OpenARDF/SignalSlinger/Software/AVR128DA28/SignalSlinger/main.cpp

/*
 *  MIT License
 *
 *  Copyright (c) 2026 DigitalConfections
 *
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
 *  THE SOFTWARE IS PROVIDED "AS IS", WITHOUT WARRANTY OF ANY KIND, EXPRESS OR
 *  IMPLIED, INCLUDING BUT NOT LIMITED TO THE WARRANTIES OF MERCHANTABILITY,
 *  FITNESS FOR A PARTICULAR PURPOSE AND NONINFRINGEMENT. IN NO EVENT SHALL THE
 *  AUTHORS OR COPYRIGHT HOLDERS BE LIABLE FOR ANY CLAIM, DAMAGES OR OTHER
 *  LIABILITY, WHETHER IN AN ACTION OF CONTRACT, TORT OR OTHERWISE, ARISING FROM,
 *  OUT OF OR IN CONNECTION WITH THE SOFTWARE OR THE USE OR OTHER DEALINGS IN THE
 *  SOFTWARE.
 */

#include "serial_latency.h"
#include "atmel_start.h"
#include <avr/io.h>
#include <avr/interrupt.h>
#include <string.h>
#include <time.h>
#include <stdio.h>
#include <stdlib.h>
#include <ctype.h>
#include <avr/sleep.h>
#include <atomic.h>
#include <math.h>

#include "serialbus.h"
#include "transmitter.h"
#include "morse.h"
#include "adc.h"
#include "external_battery_feedback.h"
#include "util.h"
#include "eeprommanager.h"
#include "binio.h"
#include "leds.h"
#include "CircularStringBuff.h"
#include "globals.h"
#include "shared_state.h"
#include "thermal_shutdown.h"
#include "session_history.h"
#include "rtc.h"
#include "rstctrl.h"

#include <cpuint.h>
#include <ccp.h>

/*
 * Main firmware orchestration for SignalSlinger.
 *
 * This module owns the top-level runtime state, interrupt handlers, event
 * engine coordination, user interaction flow, and serial command handling that
 * ties the rest of the firmware together.
 *
 * Lower-level hardware drivers and focused utility logic belong in their own
 * modules; this file is where those pieces are sequenced into device behavior.
 */

/***********************************************************************
 * Local Typedefs
 ************************************************************************/

/* Select how watchdog-related resets should be handled. */
typedef enum
{
	WD_SW_RESETS,
	WD_HW_RESETS,
	WD_FORCE_RESET,
	WD_DISABLE
} WDReset;

/* Record what caused the device to wake or start running. */
typedef enum
{
	AWAKENED_INIT,
	POWER_UP_START,
	AWAKENED_BY_CLOCK,
	AWAKENED_BY_BUTTONPRESS,
	AWAKENED_BY_SERIAL_PORT
} Awakened_t;

/* Track missing hardware discovered during startup or runtime checks. */
typedef enum
{
	HARDWARE_OK,
	HARDWARE_NO_RTC = 0x01,
	HARDWARE_NO_SI5351 = 0x02
} HardwareError_t;

static bool evaluateThermalShutdownState(float processor_temperature, bool current_state);
static uint16_t adcConversionPeriodTicks(uint8_t channel_index);
static void updateTemperatureState(float temperature);
static void turnCoolingFanOffForSleep(void);
static float sampleTemperatureNow(void);
static bool resetProcessorTemperatureExtremesToCurrent(float *temperature_out);
static bool resetProcessorMaxEverTemperatureToCurrent(float *temperature_out);

/* Track the current step in the serial cloning/synchronization exchange. */
typedef enum
{
	SYNC_Searching_for_slave,
	SYNC_Waiting_for_FUN_A_reply,
	SYNC_Align_to_Second_Transition,
	SYNC_Waiting_for_CLK_T_reply,
	SYNC_Waiting_for_CLK_S_reply,
	SYNC_Waiting_for_CLK_F_reply,
	SYNC_Waiting_for_CLK_D_reply,
	SYNC_Waiting_for_ID_reply,
	SYNC_Waiting_for_ID_CodeSpeed_reply,
	SYNC_Waiting_for_Pattern_CodeSpeed_reply,
	SYNC_Waiting_for_EVT_reply,
	SYNC_Waiting_for_NoEvent_Freq_reply,
	SYNC_Waiting_for_Freq_Low_reply,
	SYNC_Waiting_for_Freq_Med_reply,
	SYNC_Waiting_for_Freq_Hi_reply,
	SYNC_Waiting_for_Freq_Beacon_reply,
	// 	SYNC_Waiting_for_PAT_A_reply,
	// 	SYNC_Waiting_for_PAT_B_reply,
	// 	SYNC_Waiting_for_PAT_C_reply,
	// 	SYNC_Waiting_for_FRE_A_reply,
	// 	SYNC_Waiting_for_FRE_B_reply,
	// 	SYNC_Waiting_for_FRE_C_reply,
	SYNC_Waiting_for_ACK
} SyncState_t;

/* Preserve the event window that should be restored after clone mode exits. */
typedef struct
{
	time_t event_start_epoch;
	time_t event_finish_epoch;
	uint8_t days_to_run;
} CloneTimingSnapshot_t;

#define PROGRAMMING_MESSAGE_TIMEOUT_PERIOD 3000
#define WAKE_AUTH_HOLD_TICKS 600
#define BOOTLOADER_WAKE_AUTH_CREDIT_TICKS 420
#define BUTTON_HOLD_PREVIEW_SAMPLE_TICKS 50
#define BUTTON_LONG_PRESS_SAMPLE_TICKS 200
#define STARTUP_SWITCH_SETTLE_SAMPLE_COUNT 12
#define STARTUP_SWITCH_SETTLE_DELAY_MS 5
#define SIGNALSLINGER_BOOT_HANDOFF_POWER_BUTTON_HELD 0x53U
#define SIGNALSLINGER_BOOT_APP_UPDATE_REQUEST 0xA5U
#define SIGNALSLINGER_BOOT_HANDOFF_INFO_MAGIC 0xB0U
#define SIGNALSLINGER_BOOT_HANDOFF_INFO_MAGIC_MASK 0xF0U
#define SIGNALSLINGER_BOOT_HANDOFF_INFO_PROTOCOL_MASK 0x0FU
#define SIGNALSLINGER_BOOT_HANDOFF_UNAVAILABLE 0xFFU

/***********************************************************************
 * Global Variables & String Constants
 *
 * Identify each global with a "g_" prefix
 * Whenever possible limit globals' scope to this file using "static"
 * Use "volatile" for globals shared between ISRs and foreground
 ************************************************************************/
#define TEMP_STRING_SIZE 50
static char g_tempStr[TEMP_STRING_SIZE + 1] = {'\0'};
static uint8_t g_bootloader_protocol = SIGNALSLINGER_BOOT_HANDOFF_UNAVAILABLE;
static uint8_t g_bootloader_version_major = SIGNALSLINGER_BOOT_HANDOFF_UNAVAILABLE;
static uint8_t g_bootloader_version_minor = SIGNALSLINGER_BOOT_HANDOFF_UNAVAILABLE;

volatile bool g_device_enabled = false;

static volatile bool g_foreground_start_event = false;
static volatile bool g_foreground_enable_transmitter = false;
static volatile int g_hardware_error = (int)HARDWARE_OK;
static volatile bool g_defer_cloned_event_start = false;

/* Variables related to the "Event Engine" which consists of two ISRs and the foreground working
together to handle event timing. Communication between ISRs and forground is most efficiently
handled using volatile global variables. */
static volatile int32_t g_evteng_on_the_air = 0;
static volatile int g_evteng_sendID_seconds_countdown = 0;
static volatile uint16_t g_evteng_code_throttle = 50;
static volatile uint16_t g_evteng_sleepshutdown_seconds = 300;
volatile uint8_t g_evteng_id_codespeed = EEPROM_ID_CODE_SPEED_DEFAULT;
volatile uint8_t g_evteng_pattern_codespeed = EEPROM_PATTERN_CODE_SPEED_DEFAULT;
volatile int16_t g_evteng_on_air_seconds = EEPROM_ON_AIR_TIME_DEFAULT;   /* amount of time to spend on the air */
volatile int16_t g_evteng_off_air_seconds = EEPROM_OFF_AIR_TIME_DEFAULT; /* amount of time to wait before returning to the air */

/**
 * Update the system clock, optionally re-zeroing the external RTC at the same time.
 *
 * The foreground uses this helper when a clock-setting operation must keep the
 * software time base and the hardware RTC aligned through one critical section.
 *
 * @param epoch New epoch value to install.
 * @param reset_rtc true to zero the RTC counter before updating system time.
 */
static inline void atomic_set_system_time(time_t epoch, bool reset_rtc)
{
	ENTER_CRITICAL(main_set_system_time);
	if(reset_rtc)
	{
		RTC_zero();
	}
	set_system_time(epoch);
	EXIT_CRITICAL(main_set_system_time);
}
volatile int16_t g_evteng_intra_cycle_delay_time = EEPROM_INTRA_CYCLE_DELAY_TIME_DEFAULT; /* offset time into a repeating transmit cycle */
volatile int16_t g_evteng_ID_period_seconds = EEPROM_ID_TIME_INTERVAL_DEFAULT;            /* amount of time between ID/callsign transmissions */
volatile time_t g_event_start_epoch = EEPROM_START_TIME_DEFAULT;
volatile time_t g_evteng_loaded_start_epoch = 0;
volatile time_t g_event_finish_epoch = EEPROM_FINISH_TIME_DEFAULT;
volatile time_t g_evteng_loaded_finish_epoch = 0;
volatile bool g_evteng_event_enabled = EEPROM_EVENT_ENABLED_DEFAULT; /* indicates that the conditions for executing the event are set */
volatile bool g_evteng_event_commenced = false;
volatile bool g_evteng_sending_station_ID = false; /* Allows a small extension of transmissions to ensure the ID is fully sent */
static volatile bool g_evteng_run_event_until_canceled = false;
volatile bool g_evteng_initialize_event = false;

/* Various other functions handled in ISRs are most efficiently handled (with care) by volatile
globals. */
volatile float g_internal_voltage_low_threshold = EEPROM_INT_BATTERY_LOW_THRESHOLD_V;
volatile float g_internal_bat_voltage = 0.;
volatile bool g_internal_bat_detected = false;
volatile int8_t g_thermal_shutdown_threshold = EEPROM_THERMAL_SHUTDOWN_THRESHOLD_DEFAULT;
volatile bool g_thermal_shutdown_enabled = EEPROM_THERMAL_SHUTDOWN_ENABLED_DEFAULT;
volatile float g_external_voltage = 0.;
volatile float g_processor_temperature = MINIMUM_VALID_TEMP - 1.;
volatile float g_processor_min_temperature = MAXIMUM_VALID_TEMP + 1.;
volatile float g_processor_max_temperature = MINIMUM_VALID_TEMP - 1.;
volatile float g_processor_max_ever_temperature = EEPROM_PROCESSOR_MAX_EVER_TEMPERATURE_DEFAULT;
volatile bool g_restart_conversions = false;
volatile bool g_seconds_transition = false;
volatile bool g_muteAfterID = false; /* Inhibit any transmissions after the ID has been sent */
volatile uint32_t g_event_checksum = 0;
volatile uint8_t g_days_to_run = 1;
volatile uint8_t g_schedule_day_index = 0;
volatile Function_t g_function = Function_ARDF_TX;
volatile uint8_t g_foxoring_pattern_codespeed = EEPROM_FOXORING_PATTERN_CODESPEED_DEFAULT;
volatile uint16_t g_time_needed_for_ID = 0;
char g_messages_text[STATION_ID + 1][MAX_PATTERN_TEXT_LENGTH + 2];

static volatile bool g_go_to_sleep_now = false;
static volatile bool g_sleeping = false;
static volatile time_t g_time_to_wake_up = 0;
static volatile Awakened_t g_awakenedBy = POWER_UP_START;
static volatile SleepType g_sleepType = SLEEP_FOREVER;
static volatile uint8_t g_button_wake_prior_sleep_type = SLEEP_FOREVER;
static volatile bool g_button_wake_prior_event_enabled = false;
static volatile bool g_button_wake_prior_event_commenced = false;
static volatile time_t g_seconds_since_wakeup = 0;
static volatile bool g_foreground_check_for_long_wakeup_press = false;
static volatile bool g_ignore_sleep_button_wake_until_release = false;
static volatile bool g_device_wakeup_complete = false;
static volatile bool g_foreground_enable_serialbus = false;
static volatile bool g_charge_battery = false;
static volatile bool g_turn_on_fan = false;
static volatile bool g_foreground_report_settings = false;
static volatile uint16_t g_report_settings_countdown = 0;
static bool g_event_launched_by_user_action = false;
static bool g_start_event_after_keydown = false; /* Foreground-only: one-press keydown should launch a synced event afterward */

/* Foreground-only interaction helpers:
 * - g_consume_current_press_for_led_wake prevents the first press after LED timeout
 *   from being interpreted as a command.
 * - g_pending_led_revival requests that foreground restore LED indications.
 * - g_event_canceled_by_user latches cancellation of the current event window until
 *   the user explicitly restarts it or the schedule advances to a new window.
 */
static volatile bool g_consume_current_press_for_led_wake = false;
static volatile bool g_pending_led_revival = false;
static volatile bool g_event_canceled_by_user = false;
/* Calibration consumes the first debounced edge immediately so a press cannot
 * also become an event command, LED wake, multi-press, or long-hold action. */
static volatile bool g_consume_current_press_for_calibration_exit = false;
static volatile bool g_foreground_exit_calibration = false;
static volatile bool g_button_hold_preview_active = false;

/* Preserve the intent of the press even if a test expires or a scheduled start
 * arrives while the user is still holding the button. */
enum ButtonHoldIntent { BUTTON_HOLD_DEFAULT, BUTTON_HOLD_STOP_TEST, BUTTON_HOLD_SLEEP_SCHEDULE };
static volatile uint8_t g_button_hold_intent = BUTTON_HOLD_DEFAULT;
static volatile uint8_t g_long_button_hold_intent = BUTTON_HOLD_DEFAULT;

#define NUMBER_OF_POLLED_ADC_CHANNELS 3
#define ADC_CONVERSION_TIMEOUT_TICKS 10
static ADC_Active_Channel_t g_adcChannelOrder[NUMBER_OF_POLLED_ADC_CHANNELS] = {ADCInternalBatteryVoltage, ADCExternalBatteryVoltage, ADCTemperature};
static volatile uint16_t g_adcCountdownCount[NUMBER_OF_POLLED_ADC_CHANNELS] = {2000, 2000, 4000};
static volatile uint16_t g_lastConversionResult[NUMBER_OF_POLLED_ADC_CHANNELS] = {0, 0, 0};
static ExternalBatteryFeedback g_external_battery_feedback;

/* Release only the awake measurement client, preserving charge/transmit demand.
 * Called with interrupts masked at sleep entry and by the ADC service ISR.
 */
static void cancelExternalBatteryFeedback(void)
{
	g_external_battery_feedback.reset();
	setExtBatLoadSwitch(OFF, BATTERY_MEASUREMENT);
}

static volatile bool g_thermal_shutdown = false;

volatile uint16_t g_foreground_handle_counted_presses = 0;
volatile uint16_t g_switch_presses_count = 0;
volatile bool g_long_button_press = false;
volatile uint16_t g_button_hold_countdown;

#define NUMBER_OF_TEST_FREQUENCIES (4)
uint8_t g_frequency_to_test = NUMBER_OF_TEST_FREQUENCIES;

static volatile uint16_t g_programming_countdown = 0;
static volatile uint16_t g_programming_msg_throttle = 0;
static volatile uint16_t g_send_clone_success_countdown = 0;
static SyncState_t g_programming_state = SYNC_Searching_for_slave;
static CloneTimingSnapshot_t g_clone_timing_snapshot = {0, 0, 1};
volatile bool g_cloningInProgress = false;

volatile Enunciation_t g_enunciator = LED_ONLY;
static volatile uint16_t g_key_down_countdown = 0;
static volatile bool g_foreground_reset_after_keydown = false;
static volatile uint16_t g_demo_event_countdown = 0;
static volatile bool g_foreground_reset_after_demo = false;

leds LEDS = leds();
CircularStringBuff g_text_buff(TEXT_BUFF_SIZE);

EepromManager g_ee_mgr;

volatile bool g_isMaster = false;
volatile uint16_t isMasterCountdownSeconds = 0;
Fox_t g_fox[EVENT_NUMBER_OF_EVENTS] = {FOX_1, SPRINT_S1, FOXORING_FOX1}; /* classic, sprint, foxoring */

Event_t g_event = EEPROM_EVENT_SETTING_DEFAULT;
Frequency_Hz g_frequency = EEPROM_FREQUENCY_DEFAULT;
Frequency_Hz g_frequency_low = EEPROM_FREQUENCY_LOW_DEFAULT;
Frequency_Hz g_frequency_med = EEPROM_FREQUENCY_MED_DEFAULT;
Frequency_Hz g_frequency_hi = EEPROM_FREQUENCY_HI_DEFAULT;
Frequency_Hz g_frequency_beacon = EEPROM_FREQUENCY_BEACON_DEFAULT;

int8_t g_utc_offset;
uint8_t g_unlockCode[UNLOCK_CODE_SIZE + 2];

volatile bool g_enable_manual_transmissions = true;
static volatile bool g_meshmode = false;

typedef enum
{
	FREQ_SOURCE_CURRENT,
	FREQ_SOURCE_LOW,
	FREQ_SOURCE_MED,
	FREQ_SOURCE_HIGH,
	FREQ_SOURCE_BEACON
} FrequencySource_t;

static const char *const g_fixed_fox_pattern_text[USE_CURRENT_FOX] =
    {
        "MO",
        "MOE",
        "MOI",
        "MOS",
        "MOH",
        "MO5",
        "S",
        "ME",
        "MI",
        "MS",
        "MH",
        "M5",
        "OE",
        "OI",
        "OS",
        "OH",
        "O5",
        NULL,
        NULL,
        NULL,
        NULL};

static const FrequencySource_t g_fox_frequency_source[USE_CURRENT_FOX] =
    {
        FREQ_SOURCE_BEACON,
        FREQ_SOURCE_LOW,
        FREQ_SOURCE_LOW,
        FREQ_SOURCE_LOW,
        FREQ_SOURCE_LOW,
        FREQ_SOURCE_LOW,
        FREQ_SOURCE_MED,
        FREQ_SOURCE_LOW,
        FREQ_SOURCE_LOW,
        FREQ_SOURCE_LOW,
        FREQ_SOURCE_LOW,
        FREQ_SOURCE_LOW,
        FREQ_SOURCE_HIGH,
        FREQ_SOURCE_HIGH,
        FREQ_SOURCE_HIGH,
        FREQ_SOURCE_HIGH,
        FREQ_SOURCE_HIGH,
        FREQ_SOURCE_LOW,
        FREQ_SOURCE_MED,
        FREQ_SOURCE_HIGH,
        FREQ_SOURCE_LOW};

static const char *const g_frequency_test_pattern_text[NUMBER_OF_TEST_FREQUENCIES] =
    {
        "< E<",
        "< EE<",
        "< EEE<",
        "< EEEE<"};

/***********************************************************************
 * Private Function Prototypes
 *
 * These functions are available only within this file
 ************************************************************************/
void handle_1sec_tasks(void);
bool loadedEventShouldBeEnabled(void);
void handleSerialBusMsgs(void);
uint16_t throttleValue(uint8_t speed);
bool activateEventEngineUsingCurrentSettings(time_t startTime, time_t finishTime);
bool launchLoadedEvent(void);
void reportSettings(void);
uint16_t timeNeededForID(void);
Frequency_Hz getFrequencySetting(void);
bool syncCurrentFrequencySetting(bool leaveClockOff);
bool refreshCurrentFrequencySetting(Frequency_Hz previousFrequency, bool leaveClockOff);
char *getCurrentPatternText(void);
int getPatternCodeSpeed(void);
int getFoxCodeSpeed(void);
Fox_t getFoxSetting(void);
void handleSerialCloning(void);
bool timeIsSet(void);
bool eventIsScheduledToRun(time_t *start_epoch, time_t *finish_epoch);
bool eventIsScheduledToRun(volatile time_t *start_epoch, volatile time_t *finish_epoch);
bool eventIsScheduledToRunNow(time_t start_epoch, time_t finish_epoch);
bool eventScheduledForTheFuture(time_t start_epoch, time_t finish_epoch);
bool noEventWillRun(void);
bool eventRunning(void);
void restoreStateAfterButtonWakeAuthorization(void);
static void restoreEventAfterWakeAuthorization(void);
static bool shouldRestoreTransmitterForSleepContext(SleepType sleepType);
static const char *hardwareBuildString(void);
static void sendFirmwareInfo(void);
static inline void captureButtonWakeFromSleep(void);
static inline void clearPendingWakeInterruptFlags(void);
static inline void setWakeAuthorizationLedPinsOn(void);
static inline void bootloaderHandoffCaptureInfo(void);
static inline bool bootloaderHandoffReportedPowerButtonHeld(void);
static inline bool bootloaderHandoffInfoAvailable(void);
static inline bool coldStartLedFeedbackShouldStayOn(bool bootloader_power_button_held);
static inline uint16_t initialWakeAuthorizationTicks(bool bootloader_power_button_held);
static void serviceColdStartButtonDuringStartup(bool *button_held_closed);
static inline void setButtonHoldPreviewIndicator(bool active);
static void refreshProcessorMaxEverTemperature(void);
bool shouldPowerTransmitterAfterWake(void);
void configRedLEDforEvent(void);
bool switchIsClosed(void);
static inline bool rawSwitchIsClosed(void);
static bool switchIsClosedAtStartup(void);
static inline void configureSwitchInterruptForAwake(void);
static inline void configureSwitchInterruptForSleepWake(void);
bool allClocksSet(Settings_t location);
ConfigurationState_t clockConfigurationCheck(Settings_t location);
bool startEvent(void);
static bool foxUsesFastCodeSpeed(Event_t event, Fox_t fox);

/*******************************/
/* Hardcoded event support     */
/*******************************/
void suspendEvent(SessionReason reason = REASON_SETTINGS);
void startEventNow(bool configOverride);
void startSyncdEventNow(bool configOverride);
bool startEventUsingRTC(void);
void startTransmissionsNow(bool configOverride);
void setupForFox(Fox_t fox, EventAction_t action);
time_t validateTimeString(char *str, char *errMsg);
time_t validateTimeString(char *str, volatile time_t *epochVar, bool align5min, char *errMsh);
time_t validateTimeString(char *str, volatile time_t *epochVar, bool align5min, char *errMsg, const char *rawInput);
bool reportTimeTill(time_t from, time_t until, const char *prefix, const char *failMsg);
void reportConfigErrors(Settings_t location);
/*******************************/
/* End hardcoded event support */
/*******************************/

static void loadCurrentPatternMorse(bool *repeat, callerID_t caller);
static void loadStationIDMorse(bool *repeat, callerID_t caller);
static void refreshActiveAutomatedPattern(void);
static const char *completeTimeString_volatile(const char *partialString, volatile time_t *currentEpoch);
static bool parseClockHourMinuteOffset(const char *offsetString, uint16_t *hours, uint8_t *minutes, bool *hasMinutes);
static time_t alignEpochToNearestBoundary(time_t epoch, time_t boundary, time_t minimumEpoch);
static bool resolveClockOffsetToEpoch(const char *offsetString, time_t baseEpoch, const char *baseEpochError, bool suppressBaseEpochError, time_t hourBoundary, time_t minuteBoundary, time_t *resolvedEpoch, char *errMsg);
static void persistClockEpochValue(volatile time_t *loadedEpoch, volatile time_t *savedEpoch, time_t epoch, EE_var_t eeVar, void *eeValue);
static void acknowledgeClonedClockValue(const char *reply, time_t epoch);
static void clearCloneUiLatch(void);
static void reportUiDiagnostics(void);
static bool injectUiButtonPresses(const char *text);
static void finalizeLocalClockUpdate(void);
static void finalizeDisabledEventStartUpdate(void);
static bool eventFromSerialArg(char eventArg, Event_t *event);
static bool alignSavedClassicStartTimeIfNeeded(char *notice, size_t noticeSize);
static void persistFoxSettingForCurrentEvent(Fox_t fox);
static void persistFrequencyValue(EE_var_t eeVar, Frequency_Hz frequency);
static bool cancelManualTransientState(void);
static bool finishTimedEventIfExpired(time_t now);
static void captureCloneTimingSnapshot(void);
static void reinitializeEventEngine(void);
static void loadEventTimingForFox(Fox_t fox);
static void resumeLoadedEventAfterCloneExit(bool deferStartIfAlreadyRunning);
static bool reloadLoadedEventWindowFromSavedSettings(void);
static bool resyncLoadedEventWindowAfterClockSet(void);
static bool advanceLoadedEventWindowAfterCurrentDayCancel(void);
static inline void extendMasterModeTimeout(void);
static bool currentLoadedEventWindowCanceled(void);
static bool manualTestInProgress(void);
static uint8_t buttonHoldIntent(void);
static void cancelEventFromButton(void);
static bool handleScheduledButtonHold(void);
static void handleLongButtonPress(void);
static bool savedScheduleCanLimitManualRun(void);
static void configGreenLEDForCurrentState(bool internal_bat_error, float external_voltage);
#include "session_runtime.h"
#include "ui_bench.h"
static void reviveLedActivityForCurrentState(void);

/***********************************************************************
 * Interrupt Service Routines
 ************************************************************************/

/**
 * Advance one-second timekeeping and wake/sleep state.
 *
 * This ISR owns the coarse 1 Hz heartbeat. It updates system time,
 * nudges the event-engine on-air countdown toward zero, and either
 * runs foreground-safe once-per-second work or wakes the unit when a
 * sleep deadline has been reached.
 */
ISR(RTC_CNT_vect)
{
	SERIAL_LATENCY_SCOPE(LAT_RTC);
	uint8_t x = RTC.INTFLAGS;

	if(x & RTC_OVF_bm)
	{
		system_tick();

		if(g_evteng_on_the_air < 0)
		{
			g_evteng_on_the_air++;
		}
		else if(g_evteng_on_the_air > 0)
		{
			g_evteng_on_the_air--;
		}

		g_seconds_transition = true;
		if(g_temperature_fresh_seconds) --g_temperature_fresh_seconds;

		if(g_sleeping)
		{
			finishTimedEventIfExpired(time(null));
			if(g_sleepType != SLEEP_FOREVER)
			{
				time_t time_to_wake_up = atomic_read_time(&g_time_to_wake_up);
				if(g_sleepType == SLEEP_UNTIL_NEXT_XMSN)
				{
					if((g_evteng_on_the_air > -6) || (time_to_wake_up <= time(null))) /* Always wake up at least 5 seconds before showtime */
					{
						g_go_to_sleep_now = false;
						g_sleeping = false;
						g_awakenedBy = AWAKENED_BY_CLOCK;
					}
				}
				else if(g_sleepType == SLEEP_UNTIL_START_TIME)
				{
					if(time_to_wake_up <= time(null))
					{
						g_go_to_sleep_now = false;
						g_sleeping = false;
						g_awakenedBy = AWAKENED_BY_CLOCK;
					}
				}
			}
		}
		else
		{
			handle_1sec_tasks();
		}
	}

	if(x & RTC_OVF_bm) captureUiBenchTick();
	RTC.INTFLAGS = (RTC_OVF_bm | RTC_CMP_bm);
}

/**
 * Run high-rate event-engine and input-service work.
 *
 * This 300 Hz ISR handles Morse timing, pushbutton sampling, ADC
 * scheduling/completion, and other short-latency state updates that
 * would be too jitter-sensitive for the foreground loop.
 */
ISR(TCB0_INT_vect)
{
	SERIAL_LATENCY_SCOPE(LAT_TCB0);
	static uint8_t fiftyMS = 6;
	static bool on_air_finished = false;
	static bool transitionPrepped = false;
	static int idTimeout = 0;
	static bool id_timed_out = false;
	static uint16_t codeInc = 0;
	static bool muteAfterID = false; /* Inhibit any transmissions immediately after the ID has been sent */
	static bool key = false;

	if(g_evteng_initialize_event)
	{
		g_evteng_initialize_event = false;
		on_air_finished = false;
		transitionPrepped = false;
		idTimeout = 0;
		id_timed_out = false;
		codeInc = 0;
		muteAfterID = false;
		key = OFF;
		g_evteng_sending_station_ID = false;
	}

	uint8_t x = TCB0.INTFLAGS;

	if(x & TCB_CAPT_bm)
	{
		static bool conversionInProcess = false;
		static int8_t indexConversionInProcess = 0;
		static uint16_t adcConversionWaitTicks = 0;
		bool repeat, finished;
		static uint16_t switch_closures_count_period = 40;
		uint8_t holdSwitch = 0;
		static uint8_t buttonReleased = false;
		static uint8_t longPressEnabled = true;
		static uint16_t switch_closed_time = 0;
		static bool consumeHeldPreviewPress = false;
		static bool wakeAuthSwitchClosed = true;

		if(g_key_down_countdown)
		{
			g_key_down_countdown--;

			if(!g_key_down_countdown)
			{
				g_foreground_reset_after_keydown = true;
			}
		}

		if(g_button_hold_countdown)
		{
			g_button_hold_countdown--;
		}

		if(g_demo_event_countdown)
		{
			g_demo_event_countdown--;

			if(!g_demo_event_countdown)
			{
				g_foreground_reset_after_demo = true;
			}
		}

		if(g_report_settings_countdown)
		{
			g_report_settings_countdown--;

			if(!g_report_settings_countdown)
			{
				g_foreground_report_settings = true;
			}
		}

		/* Handle pushbutton press detection */

		if(g_device_wakeup_complete)
		{
			fiftyMS++;
			/* Sample the pushbutton once every 6 TCB0 periods (nominally 20 ms). */
			if(!(fiftyMS % 6))
			{
				holdSwitch = portDdebouncedVals() & (1 << SWITCH);
				debounce();
				uint8_t switchNow = portDdebouncedVals() & (1 << SWITCH);
				applyUiButtonSample(&holdSwitch, &switchNow);

				if(holdSwitch != switchNow) /* Change detected */
				{
					if(holdSwitch) /* Switch was open, so it must have just now closed */
					{
						if(txCalibrationCarrierActive())
						{
							g_consume_current_press_for_calibration_exit = true;
							g_foreground_exit_calibration = true;
							g_switch_presses_count = 0;
							buttonReleased = false;
							switch_closures_count_period = 0;
							switch_closed_time = 0;
							longPressEnabled = false;
							consumeHeldPreviewPress = false;
							setButtonHoldPreviewIndicator(false);
						}
						/* If the unit is awake but the LEDs have timed out, the first press only
						 * revives LED activity and must not be interpreted as a command. */
						else if(!g_sleeping && !LEDS.active())
						{
							g_button_hold_intent = buttonHoldIntent();
							g_consume_current_press_for_led_wake = true;
							g_pending_led_revival = true;
							g_switch_presses_count = 0;
							buttonReleased = false;
							switch_closures_count_period = 0;
							switch_closed_time = 0;
							longPressEnabled = false;
							consumeHeldPreviewPress = false;
							setButtonHoldPreviewIndicator(false);
						}
						else
						{
							g_button_hold_intent = buttonHoldIntent();
							g_switch_presses_count++;
							buttonReleased = false;
							switch_closures_count_period = 40;
							consumeHeldPreviewPress = false;
						}
					}
					else /* Switch is now open */
					{
						switch_closed_time = 0;
						buttonReleased = true;
						if(g_consume_current_press_for_calibration_exit)
						{
							g_consume_current_press_for_calibration_exit = false;
							longPressEnabled = true;
							g_switch_presses_count = 0;
							switch_closures_count_period = 0;
						}
						else if(consumeHeldPreviewPress)
						{
							setButtonHoldPreviewIndicator(false);
							consumeHeldPreviewPress = false;
							longPressEnabled = true;
							g_switch_presses_count = 0;
							switch_closures_count_period = 0;
						}
						else if(g_consume_current_press_for_led_wake)
						{
							g_consume_current_press_for_led_wake = false;
							longPressEnabled = true;
							g_switch_presses_count = 0;
							switch_closures_count_period = 0;
						}
						else
						{
							longPressEnabled = true;
						}
					}
				}
				else if(!holdSwitch) // && LEDS.active()) /* Switch closed, LEDs operating */
				{
					if(!g_consume_current_press_for_led_wake && !g_long_button_press && longPressEnabled)
					{
						if(++switch_closed_time >= BUTTON_LONG_PRESS_SAMPLE_TICKS)
						{
							setButtonHoldPreviewIndicator(false);
							consumeHeldPreviewPress = false;
							g_long_button_hold_intent = g_button_hold_intent;
							g_long_button_press = true;
							switch_closed_time = 0;
							g_switch_presses_count = 0;
							switch_closures_count_period = 0;
							longPressEnabled = false;
						}
						else if((switch_closed_time >= BUTTON_HOLD_PREVIEW_SAMPLE_TICKS) && !consumeHeldPreviewPress)
						{
							setButtonHoldPreviewIndicator(true);
							consumeHeldPreviewPress = true;
							g_switch_presses_count = 0;
							switch_closures_count_period = 0;
						}
					}
				}

				if(g_consume_current_press_for_led_wake)
				{
					g_switch_presses_count = 0;
				}
				else if(switch_closures_count_period) // Time to check if button presses have occurred
				{
					static uint8_t hold_switch_presses_count = 0;
					switch_closures_count_period--;

					if((g_switch_presses_count != 1) || buttonReleased) // Special case: the first press could be a long press if pushbutton is held long enough
					{
						if(!switch_closures_count_period) // Time's up - examine how many button presses were counted
						{
							if(g_switch_presses_count && (g_switch_presses_count <= MAXIMUM_NUM_OF_KEYPRESSES))
							{
								g_foreground_handle_counted_presses = g_switch_presses_count;
							}

							g_switch_presses_count = 0;
							hold_switch_presses_count = 0;
						}
						else if(g_switch_presses_count != hold_switch_presses_count) // New press detected - wait a while longer to see if there's another one
						{
							hold_switch_presses_count = g_switch_presses_count;
							switch_closures_count_period = 40;
						}
					}
				}
				else if(g_switch_presses_count == 1 && buttonReleased)
				{
					switch_closures_count_period = 40;
				}
				else if(g_switch_presses_count > MAXIMUM_NUM_OF_KEYPRESSES) // Too many button presses - ignore them entirely
				{
					g_switch_presses_count = 0;
				}
			}
		}
		else
		{
			if(g_foreground_check_for_long_wakeup_press)
			{
				/* Foreground can spend a while finishing wake-up or cold-start
				 * work before it reevaluates the hold-to-wake state. Keep the
				 * fast authorization blink aligned with the debounced switch
				 * during that window so releasing the button stops the blink
				 * promptly without changing whether the wake was already earned.
				 */
				debounce();
				bool switchClosed = !(portDdebouncedVals() & (1 << SWITCH));
				if(switchClosed != wakeAuthSwitchClosed)
				{
					wakeAuthSwitchClosed = switchClosed;
					LEDS.setWakeAuthorizationBlink(switchClosed);
				}
			}
			else
			{
				wakeAuthSwitchClosed = true;
			}

			clearUiButtonInjection();
			longPressEnabled = false;
			switch_closed_time = 0;
			g_switch_presses_count = 0;
			g_consume_current_press_for_led_wake = false;
			consumeHeldPreviewPress = false;
			setButtonHoldPreviewIndicator(false);
			//			switch_closures_count_period = 0;
			g_long_button_press = false;
		}

		if(g_programming_countdown > 0)
			g_programming_countdown--;
		if(g_programming_msg_throttle)
			g_programming_msg_throttle--;
		if(g_send_clone_success_countdown)
			g_send_clone_success_countdown--;

		if(idTimeout)
		{
			idTimeout--;

			if(!idTimeout)
			{
				id_timed_out = true;
			}
		}

		if(g_go_to_sleep_now)
		{
			/* A foreground shutdown request may spend a short time printing status
			 * before the later sleep-entry block deactivates the LEDs entirely.
			 * Keep the ISR from reasserting red LED/keying state during that tail.
			 */
			key = OFF;
			keyTransmitter(OFF);
			LEDS.setRed(OFF);
		}
		else if(g_evteng_event_enabled && g_evteng_event_commenced && !g_isMaster) /* Handle cycling transmissions */
		{
			if((g_evteng_on_the_air > 0) || (g_evteng_sending_station_ID && !id_timed_out) || (!g_evteng_off_air_seconds))
			{
				on_air_finished = true;

				transitionPrepped = false;

				/* Interrupt transmissions and send the ID under these conditions */
				if(!g_evteng_sending_station_ID && (!g_evteng_off_air_seconds || (g_evteng_on_the_air <= g_time_needed_for_ID)) && !g_evteng_sendID_seconds_countdown && g_time_needed_for_ID) /* Time to identify on the air */
				{
					g_evteng_code_throttle = throttleValue(g_evteng_id_codespeed);
					repeat = false;
					loadStationIDMorse(&repeat, CALLER_AUTOMATED_EVENT); /* Send only once */
					g_evteng_sending_station_ID = true;
					idTimeout = g_evteng_code_throttle << 2;
					id_timed_out = false;
					g_evteng_sendID_seconds_countdown = g_evteng_ID_period_seconds;
					codeInc = g_evteng_code_throttle;
				}

				if(codeInc)
				{
					codeInc--;

					if(!codeInc)
					{
						key = makeMorse(NULL, &repeat, &finished, CALLER_AUTOMATED_EVENT);

						if(!repeat && finished) /* ID has completed or timed out, so resume pattern */
						{
							g_evteng_code_throttle = throttleValue(getFoxCodeSpeed());
							repeat = true;
							loadCurrentPatternMorse(&repeat, CALLER_AUTOMATED_EVENT);
							muteAfterID = g_evteng_sending_station_ID && g_evteng_off_air_seconds;
							g_evteng_sending_station_ID = false;
							idTimeout = 0;
							id_timed_out = false;

							if(!g_evteng_off_air_seconds)
							{
								g_evteng_on_the_air = g_evteng_on_air_seconds;
							}
						}

						codeInc = g_evteng_code_throttle;
					}
				}
				else
				{
					codeInc = g_evteng_code_throttle;
				}

				if(muteAfterID)
				{
					key = OFF;
				}

				keyTransmitter(key);
				LEDS.setRed(key);
			}
			else if(g_evteng_on_the_air < 0)
			{
				transitionPrepped = false;
			}
			else if(!g_evteng_on_the_air)
			{
				if(!transitionPrepped)
				{
					transitionPrepped = true;
					id_timed_out = false;

					if(on_air_finished)
					{
						on_air_finished = false;
						keyTransmitter(OFF);
						key = OFF;

						g_evteng_on_the_air = -g_evteng_off_air_seconds;
						/* Enable sleep during off-the-air periods */
						int32_t timeRemaining = SECONDS_24H; // Any  big number will do;
						time_t temp_time = time(null);

						if(timeIsSet() && !g_evteng_run_event_until_canceled)
						{
							time_t loaded_start_epoch;
							time_t loaded_finish_epoch;
							atomic_read_time_pair(&g_evteng_loaded_start_epoch, &g_evteng_loaded_finish_epoch, &loaded_start_epoch, &loaded_finish_epoch);
							if((temp_time < loaded_finish_epoch) && (loaded_start_epoch != loaded_finish_epoch))
							{
								timeRemaining = timeDif(loaded_finish_epoch, temp_time);
							}
						}

						/* Don't sleep for the last cycle to ensure that the event doesn't end while
						 * the transmitter is sleeping - which can cause problems with loading the next event */
						if(timeRemaining > (g_evteng_off_air_seconds + g_evteng_on_air_seconds + 15))
						{
							//							if(timeIsSet() && (g_evteng_off_air_seconds > 15)) /* Don't bother to sleep if the off-air time is short or we don't know what time it is */
							if(g_evteng_off_air_seconds > 15) /* Don't bother to sleep if the off-air time is short */
							{
								time_t seconds_to_sleep = (time_t)(g_evteng_off_air_seconds - 10); // Wake up 10 seconds before it is time to transmit again
								g_time_to_wake_up = temp_time + seconds_to_sleep;                  // Set the time to wake up
								g_sleepType = SLEEP_UNTIL_NEXT_XMSN;
								g_go_to_sleep_now = true;
								g_evteng_sendID_seconds_countdown = MAX(0, g_evteng_ID_period_seconds - (int)seconds_to_sleep);
							}
						}

						muteAfterID = false;
						g_evteng_sending_station_ID = false;
						idTimeout = 0;
						id_timed_out = false;

						/* Resume normal pattern */
						g_evteng_code_throttle = throttleValue(getFoxCodeSpeed());
						repeat = true;
						loadCurrentPatternMorse(&repeat, CALLER_AUTOMATED_EVENT); /* Reset pattern to start */
						LEDS.setRed(OFF);
					}
					else /* Off-the-air period just finished, or the event just began while off the air */
					{
						g_evteng_on_the_air = g_evteng_on_air_seconds;
						g_evteng_code_throttle = throttleValue(getFoxCodeSpeed());
						repeat = true;
						loadCurrentPatternMorse(&repeat, CALLER_AUTOMATED_EVENT);
						codeInc = g_evteng_code_throttle;
					}
				}
			}
		}
		else if(g_enable_manual_transmissions) /* Handle single-character transmissions */
		{
			static bool charFinished = true;
			static bool idle = true;
			bool sendBuffEmpty = text_buff_empty_atomic();
			repeat = false;

			if(lastMorseCaller() != CALLER_MANUAL_TRANSMISSIONS)
			{
				text_buff_reset_atomic();
				sendBuffEmpty = true;
				charFinished = true;
				makeMorse((char *)"\0", &repeat, null, CALLER_MANUAL_TRANSMISSIONS);
			}

			if(sendBuffEmpty && charFinished)
			{
				if(!idle)
				{
					if(key)
					{
						key = OFF;
						keyTransmitter(OFF);
						LEDS.setRed(OFF);
					}

					codeInc = g_evteng_code_throttle;
					idle = true;
				}
			}
			else
			{
				idle = false;

				if(codeInc)
				{
					codeInc--;

					if(!codeInc)
					{
						key = makeMorse(null, &repeat, &charFinished, CALLER_MANUAL_TRANSMISSIONS);

						if(charFinished) /* Completed, send next char */
						{
							static char cc[2]; /* Must be static because makeMorse saves only a pointer to the character array */
							if(text_buff_try_get_atomic(&cc[0]))
							{
								g_evteng_code_throttle = throttleValue(getPatternCodeSpeed());
								cc[1] = '\0';
								makeMorse(cc, &repeat, null, CALLER_MANUAL_TRANSMISSIONS);
								key = makeMorse(null, &repeat, &charFinished, CALLER_MANUAL_TRANSMISSIONS);
							}
						}

						if(g_enunciator == LED_AND_RF)
							keyTransmitter(key);
						LEDS.setRed(key);
						codeInc = g_evteng_code_throttle;
					}
				}
				else
				{
					if(g_enunciator == LED_AND_RF)
						keyTransmitter(key);
					LEDS.setRed(key);
					codeInc = g_evteng_code_throttle;
				}
			}
		}

		bool priorProbe = g_external_battery_feedback.probeRequested();
		g_external_battery_feedback.tick(
		    g_device_wakeup_complete && !g_sleeping && !g_go_to_sleep_now,
		    LEDS.active(), g_enable_external_battery_control, externalBatteryPowerRequested());
		if(priorProbe != g_external_battery_feedback.probeRequested())
		{
			setExtBatLoadSwitch(g_external_battery_feedback.probeRequested(), BATTERY_MEASUREMENT);
		}

		/**
		 * Handle Periodic ADC Readings
		 * The following algorithm allows multiple ADC channel readings to be performed at different polling intervals. */
		if(!conversionInProcess || g_restart_conversions)
		{
			if(g_restart_conversions && conversionInProcess && indexConversionInProcess >= 0)
			{
				// Retry a conversion displaced by a foreground status read.
				g_adcCountdownCount[indexConversionInProcess] = 0;
			}
			/* Note: countdowns will pause while a conversion is in process. Conversions are so fast that this should not be an issue though. */
			indexConversionInProcess = -1;
			conversionInProcess = false;
			adcConversionWaitTicks = 0;
			g_restart_conversions = false;

			for(uint8_t i = 0; i < NUMBER_OF_POLLED_ADC_CHANNELS; i++)
			{
				if(g_adcChannelOrder[i] == ADCExternalBatteryVoltage)
				{
					// Reuse this scheduler and converter; never sample a disconnected supply.
					if(g_external_battery_feedback.sampleDue())
					{
						indexConversionInProcess = (int8_t)i;
						break;
					}
					continue;
				}

				if(g_adcCountdownCount[i])
				{
					g_adcCountdownCount[i]--;
				}

				if(g_adcCountdownCount[i] == 0)
				{
					indexConversionInProcess = (int8_t)i;
					break;
				}
			}

			if(indexConversionInProcess >= 0)
			{
				g_adcCountdownCount[indexConversionInProcess] = adcConversionPeriodTicks(indexConversionInProcess); /* reset the tick countdown */
				ADC0_setADCChannel(g_adcChannelOrder[indexConversionInProcess]);
				ADC0_startConversion();
				conversionInProcess = true;
				adcConversionWaitTicks = 0;
			}
		}
		else if(ADC0_conversionDone()) /* wait for conversion to complete */
		{
			uint16_t hold = ADC0_read();

			if(hold < 4090)
			{
				g_lastConversionResult[indexConversionInProcess] = hold;

				if(g_adcChannelOrder[indexConversionInProcess] == ADCInternalBatteryVoltage)
				{
					float val = (0.00725 * (float)g_lastConversionResult[indexConversionInProcess]) + 0.05;
					float delta = fabs(g_internal_bat_voltage - val);

					if(delta > .1)
					{
						g_internal_bat_voltage = val;
					}
					else
					{
						g_internal_bat_voltage = (20. * g_internal_bat_voltage + val) / 21.;
					}

					g_internal_bat_detected = (g_internal_bat_voltage > INT_BAT_PRESENT_VOLTAGE);
				}
				else if(g_adcChannelOrder[indexConversionInProcess] == ADCExternalBatteryVoltage)
				{
					if(g_external_battery_feedback.sampleDue() &&
					   (!g_enable_external_battery_control || getExtBatLSEnable()))
					{
						g_external_voltage = (0.00725 * (float)g_lastConversionResult[indexConversionInProcess]) + 0.05;
					}
				}
				else if(g_adcChannelOrder[indexConversionInProcess] == ADCTemperature)
				{
					float temp = temperatureCfromADC(hold);
					updateTemperatureState(temp);
				}
			}
			else if(g_adcChannelOrder[indexConversionInProcess] == ADCTemperature) g_temperature_fresh_seconds = 0;

			if(g_adcChannelOrder[indexConversionInProcess] == ADCExternalBatteryVoltage)
			{
				g_external_battery_feedback.complete();
				setExtBatLoadSwitch(OFF, BATTERY_MEASUREMENT);
			}

			conversionInProcess = false;
			adcConversionWaitTicks = 0;
		}
		else if(++adcConversionWaitTicks >= ADC_CONVERSION_TIMEOUT_TICKS)
		{
			if(indexConversionInProcess >= 0 && g_adcChannelOrder[indexConversionInProcess] == ADCTemperature) g_temperature_fresh_seconds = 0;
			if(indexConversionInProcess >= 0 && g_adcChannelOrder[indexConversionInProcess] == ADCExternalBatteryVoltage)
			{
				g_external_battery_feedback.complete();
				setExtBatLoadSwitch(OFF, BATTERY_MEASUREMENT);
			}
			/* A missed ADC completion must not wedge periodic temperature sampling. */
			if((indexConversionInProcess >= 0) && (indexConversionInProcess < NUMBER_OF_POLLED_ADC_CHANNELS))
			{
				g_adcCountdownCount[indexConversionInProcess] = 0;
			}
			conversionInProcess = false;
			adcConversionWaitTicks = 0;
			g_restart_conversions = true;
		}
	}

	TCB0.INTFLAGS = (TCB_CAPT_bm | TCB_OVF_bm); /* clear all interrupt flags */
}

/**
 * Handle pushbutton-driven wake and serialbus-enable requests.
 *
 * While asleep, the switch can wake the unit and restore the prior
 * sleep/event context. While awake, a press is treated as a request to
 * bring the serial interface back online.
 */
ISR(PORTD_PORT_vect)
{
	uint8_t x = VPORTD.INTFLAGS;

	if(x & (1 << SWITCH))
	{
		if(g_sleeping)
		{
			if(g_ignore_sleep_button_wake_until_release)
			{
				if(!rawSwitchIsClosed())
				{
					g_ignore_sleep_button_wake_until_release = false;
					configureSwitchInterruptForSleepWake();
				}
				else
				{
					g_ignore_sleep_button_wake_until_release = false;
					captureButtonWakeFromSleep();
				}
			}
			else if(rawSwitchIsClosed())
			{
				captureButtonWakeFromSleep();
			}
		}
		else if(!sb_enabled())
		{
			g_foreground_enable_serialbus = true;
			atomic_write_u16(&g_evteng_sleepshutdown_seconds, 300);
		}
	}

	VPORTD.INTFLAGS = 0xFF; /* Clear all flags */
}

/**
 * Wake the unit when serial activity arrives during sleep.
 *
 * The RX pin interrupt is only armed while asleep. Once it fires, the
 * ISR disables the edge interrupt and lets the foreground re-enable the
 * serialbus stack after wake-up.
 */
ISR(PORTC_PORT_vect)
{
	uint8_t x = VPORTC.INTFLAGS;

	if(x & (1 << SERIAL_RX))
	{
		PORTC_pin_set_isc(SERIAL_RX, PORT_ISC_INTDISABLE_gc); // disable this interrupt

		if(g_sleeping)
		{
			g_go_to_sleep_now = false;
			g_sleeping = false;
			g_awakenedBy = AWAKENED_BY_SERIAL_PORT;
			g_foreground_enable_serialbus = true;
			atomic_write_u16(&g_evteng_sleepshutdown_seconds, 300);
		}
	}

	VPORTC.INTFLAGS = 0xFF; /* Clear all flags */
}

/**
 * Initialize hardware, restore persisted settings, and run the
 * foreground control loop.
 *
 * Startup performs the one-time bring-up that is too bulky for the
 * ISRs, then the forever loop arbitrates sleep, charging, user
 * interaction, and event control.
 *
 * @return Never returns.
 */
int main(void)
{
	bool buttonHeldClosed = false;
	bool internal_bat_error = false;
	bool startup_should_behave_as_poweroff = false;
	bool bootloader_power_button_held = false;

	atmel_start_init();
	bootloaderHandoffCaptureInfo();
	bootloader_power_button_held = bootloaderHandoffReportedPowerButtonHeld();
	configureSwitchInterruptForAwake();
	serialbus_init(SB_BAUD, SERIALBUS_USART);
	LEDS.blink(LEDS_OFF, true);
	if(coldStartLedFeedbackShouldStayOn(bootloader_power_button_held))
	{
		setWakeAuthorizationLedPinsOn();
	}
	buttonHeldClosed = bootloader_power_button_held || switchIsClosedAtStartup();
	g_foreground_check_for_long_wakeup_press = buttonHeldClosed;

	/* Register the EEPROM-backed variables before reading persisted values. */
	g_ee_mgr.initializeEEPROMVars();

	g_ee_mgr.readNonVols();
	restoreSessionHistory();
	sampleTemperatureNow();
	/* Rebuild the currently loaded event window from the saved settings. */
	reloadLoadedEventWindowFromSavedSettings();
	g_isMaster = false; /* Never start up as master */

	if(g_enable_external_battery_control)
		setExtBatLoadSwitch(ON, INITIALIZE_LS); // Enable external power

	if(g_frequency == EEPROM_FREQUENCY_DEFAULT)
	{
		g_frequency = getFrequencySetting();
		txSetFrequency(&g_frequency, true);
	}

	RTC_set_calibration(g_clock_calibration);

	if(g_foreground_check_for_long_wakeup_press)
	{
		LEDS.init();
		LEDS.setWakeAuthorizationBlink(true);
		atomic_write_u16(&g_button_hold_countdown, initialWakeAuthorizationTicks(bootloader_power_button_held));
	}

	while(util_delay_ms(2500))
	{
		serviceColdStartButtonDuringStartup(&buttonHeldClosed);
	} /* Avoid possible race conditions with peripheral devices powering up */

	reportSettings();

	/* Check that the RTC is running */
	atomic_set_system_time(YEAR_2000_EPOCH, false);
	time_t now = time(null);
	while((util_delay_ms(4500)) && (now == time(null)))
	{
		serviceColdStartButtonDuringStartup(&buttonHeldClosed);
	}

	if(now == time(null))
	{
		/* Keep the wake-authorization blink active through cold-start bring-up so
		 * its end still lines up with the eventual "* Awake" transition.
		 */
		if(coldStartLedFeedbackShouldStayOn(bootloader_power_button_held))
		{
			setWakeAuthorizationLedPinsOn();
		}
		else if((g_awakenedBy != POWER_UP_START) || !g_foreground_check_for_long_wakeup_press)
		{
			LEDS.blink(LEDS_GREEN_OFF); // Signal that the first attempt failed
			LEDS.blink(LEDS_RED_OFF);
		}
		while((util_delay_ms(3000)) && (now == time(null)))
		{
			serviceColdStartButtonDuringStartup(&buttonHeldClosed);
		}
	}

	sb_send_string(TEXT_RESET_OCCURRED_TXT);

	if(!g_device_enabled)
	{
		sb_send_string(TEXT_DEVICE_DISABLED_TXT);
	}

	if(now == time(null))
	{
		g_hardware_error |= (int)HARDWARE_NO_RTC;
		RTC_init_backup();
	}

	int tries = 5;
	/* Power the transmitter briefly so the firmware can detect whether the
	 * frequency generator responded during startup.
	 */
	powerToTransmitter(ON);

	while(tries && (!txIsInitialized()))
	{
		--tries;
		powerToTransmitter(ON);
	}

	if(!txIsInitialized())
	{
		g_hardware_error |= (int)HARDWARE_NO_SI5351;
	}

	g_evteng_run_event_until_canceled = false;
	g_foreground_start_event = g_device_enabled && loadedEventShouldBeEnabled(); /* Start any event stored in EEPROM */

	atomic_write_u16(&g_evteng_sleepshutdown_seconds, 300);

	/* Disable automatic ADC readings so startup can take synchronized voltage
	 * samples before the periodic conversion loop resumes.
	 */
	TCB0.INTCTRL = 0; /* Capture or Timeout: disable interrupts */
	TCB0.CTRLA = 0;   /* Disable timer */
	/* The external battery control load switch is initialized to ON, so we don't need to set it here */
	float internal_bat_voltage_startup = readVoltage(ADCInternalBatteryVoltage);
	float external_voltage_startup = readVoltage(ADCExternalBatteryVoltage);
	atomic_write_float(&g_internal_bat_voltage, internal_bat_voltage_startup);
	atomic_write_float(&g_external_voltage, external_voltage_startup);
	float internal_voltage_low_threshold_startup = atomic_read_float(&g_internal_voltage_low_threshold);

	g_internal_bat_detected = (internal_bat_voltage_startup > INT_BAT_PRESENT_VOLTAGE);

	if(g_internal_bat_detected && (internal_bat_voltage_startup < internal_voltage_low_threshold_startup) && (g_enable_external_battery_control > 0)) // An internal battery is present & not fully charged & charging from an external battery is enabled
	{
		g_charge_battery = true;
		setExtBatLoadSwitch(ON, INTERNAL_BATTERY_CHARGING);
	}

	g_restart_conversions = true;
	TIMERB_init();
	powerToTransmitter(OFF);

	/* Cold-start authorization should begin only after startup bring-up has
	 * completed. Re-arm the wake-auth blink and restart its countdown here so
	 * "fast blink stopped" means the unit is actually ready to stay awake when
	 * the button is released.
	 */
	if(g_awakenedBy == POWER_UP_START)
	{
		if(coldStartLedFeedbackShouldStayOn(bootloader_power_button_held))
		{
			setWakeAuthorizationLedPinsOn();
		}
		g_foreground_check_for_long_wakeup_press = g_foreground_check_for_long_wakeup_press || switchIsClosedAtStartup();
		if(g_foreground_check_for_long_wakeup_press)
		{
			LEDS.init();
			LEDS.setWakeAuthorizationBlink(true);
			uint16_t countdown = atomic_read_u16(&g_button_hold_countdown);
			uint16_t startup_countdown = initialWakeAuthorizationTicks(bootloader_power_button_held);
			if(countdown > startup_countdown)
			{
				atomic_write_u16(&g_button_hold_countdown, startup_countdown);
			}
		}
	}

	/* A cold start with no valid clock should fall back to the "power off"
	 * behavior once startup bring-up has completed, but only after the final
	 * startup switch sample has had a chance to recognize a held power button.
	 */
	startup_should_behave_as_poweroff = (g_awakenedBy == POWER_UP_START) && !g_foreground_check_for_long_wakeup_press && !timeIsSet();

	if(startup_should_behave_as_poweroff)
	{
		suspendEvent();
		g_go_to_sleep_now = true;
	}

	while(1)
	{
		flushSessionHistory();
		noteSessionStarted();
		refreshProcessorMaxEverTemperature();

		if(g_foreground_enable_serialbus)
		{
			g_foreground_enable_serialbus = false;
			if(!sb_enabled())
			{
				serialbus_init(SB_BAUD, SERIALBUS_USART);
				serialbus_set_rx_accepting_input(true);
			}
		}

		if(g_foreground_check_for_long_wakeup_press)
		{
			bool countdown_complete = !atomic_read_u16(&g_button_hold_countdown);
			bool button_wake_authorization_earned =
			    (g_awakenedBy == AWAKENED_BY_BUTTONPRESS) && countdown_complete;

			/* Once the authorization countdown has completed, treat the wake as
			 * successful even if the user releases the button before foreground
			 * reaches this branch again for button-wake resumes. During initial
			 * power-up, still require the button to be held at the moment we
			 * actually transition into the awake state.
			 */
			buttonHeldClosed = switchIsClosed();

			if(button_wake_authorization_earned ||
			   ((g_awakenedBy == POWER_UP_START) && countdown_complete && buttonHeldClosed)) /* Pushbutton held down long enough; power up */
			{
				g_long_button_press = false;
				g_foreground_check_for_long_wakeup_press = false;
				g_go_to_sleep_now = false;
				LEDS.setWakeAuthorizationBlink(false);

				/* Reassert the main power latch at the exact moment the wake-auth
				 * blink ends so releasing the pushbutton immediately afterward is
				 * guaranteed to leave the unit powered.
				 */
				PORTA_set_pin_dir(POWER_ENABLE, PORT_DIR_OUT);
				PORTA_set_pin_level(POWER_ENABLE, HIGH);

				if(g_enable_external_battery_control)
				{
					/* Restore only the charging client here. Any transmitter-side
					 * need is restored separately by the wake power-state logic so
					 * the shared auxiliary switch cannot remain latched on by a
					 * stale initialization request.
					 */
					setExtBatLoadSwitch(g_charge_battery, INTERNAL_BATTERY_CHARGING);
				}

				restoreEventAfterWakeAuthorization();

				atomic_write_u16(&g_demo_event_countdown, 0);
				g_foreground_reset_after_demo = false;
				atomic_write_u16(&g_key_down_countdown, 0);
				g_foreground_reset_after_keydown = false;
				serialbus_set_rx_accepting_input(true);

				reviveLedActivityForCurrentState();
				if(!g_meshmode)
				{
					sb_send_NewLine();
					sb_send_string(TEXT_NOT_SLEEPING_TXT);
				}

				if(!g_device_enabled)
				{
					sb_send_string(TEXT_DEVICE_DISABLED_TXT);
				}
#ifdef TEST_MODE_SOFTWARE
				sb_send_string(TEXT_TEST_SOFTWARE_NOTICE_TXT);
#endif

				if(!g_meshmode)
					sb_send_NewPrompt();
			}
			else if(!buttonHeldClosed) /* Pushbutton not held; go back to sleep */
			{
				g_go_to_sleep_now = true;
				g_foreground_check_for_long_wakeup_press = false;
				atomic_write_u16(&g_foreground_handle_counted_presses, 0);
				LEDS.setWakeAuthorizationBlink(false);
				LEDS.blink(LEDS_OFF);
			}
			else /* Spin your wheels waiting for above condition to test true */
			{
				LEDS.setWakeAuthorizationBlink(true);
			}
		}
		else
		{
			float internal_bat_voltage = atomic_read_float(&g_internal_bat_voltage);
			float external_voltage = atomic_read_float(&g_external_voltage);
			float internal_voltage_low_threshold = atomic_read_float(&g_internal_voltage_low_threshold);
			time_t seconds_since_wakeup = atomic_read_time(&g_seconds_since_wakeup);

			/* Decide whether the internal battery should be charged from the
			 * external source, if one is present.
			 */
			if((internal_bat_voltage > INT_BAT_PRESENT_VOLTAGE) && (external_voltage > EXT_BAT_CHARGE_SUPPORT_THRESH_LOW))
			{
				if(internal_bat_voltage < internal_voltage_low_threshold) // An adequate external voltage is present and an internal battery is present & not fully charged
				{
					g_charge_battery = true;
				}
				else if(internal_bat_voltage > INT_BAT_CHARGE_THRES_HIGH)
				{
					g_charge_battery = false;
				}
			}
			else
			{
				g_charge_battery = false;
			}

			if(g_enable_external_battery_control)
			{
				if(seconds_since_wakeup > 10)
				{
					setExtBatLoadSwitch(g_charge_battery, INTERNAL_BATTERY_CHARGING);
				}
			}

			handleThermalSession();
			if(g_thermal_shutdown) // Extremely high temperature detected
			{
#ifdef HW_TARGET_3_5
				setCoolingFanLSEnable(ON); // should already be on
#else
				if(!g_enable_external_battery_control && !getExtBatLSEnable())
				{
					setExtBatLoadSwitch(ON, INITIALIZE_LS);
				}
#endif
				/* The thermal latch clears only after a valid, cool measurement.
				 * handleThermalSession records each pause once and preserves its finish. */
			}
			else
			{
#ifdef HW_TARGET_3_5
				/* Newer hardware has a dedicated fan-control output that is independent of
				 * the auxiliary external-battery switch. */
				if(g_turn_on_fan)
				{
					setCoolingFanLSEnable(ON);
				}
				else
				{
					setCoolingFanLSEnable(OFF);
				}
#else
				/* Legacy hardware reuses the shared auxiliary switch as fan drive whenever
				 * external-battery control is disabled at runtime. */
				if(!g_enable_external_battery_control && g_turn_on_fan)
				{
					if(!getExtBatLSEnable())
					{
						setExtBatLoadSwitch(ON, INITIALIZE_LS);
					}
				}
				else if(!g_enable_external_battery_control)
				{
					if(getExtBatLSEnable())
					{
						setExtBatLoadSwitch(OFF, INITIALIZE_LS);
					}
				}
#endif
			}

			/* Handle transitions into and out of standby sleep. */
			if(g_go_to_sleep_now && !g_cloningInProgress && !sessionCooling() && !g_thermal_start_pending)
			{
				bool enterSleep = true;

				if(g_sleepType == SLEEP_AFTER_EVENT)
				{
					if(g_evteng_event_enabled)
					{
						enterSleep = false;
						g_go_to_sleep_now = false;
						atomic_write_u16(&g_evteng_sleepshutdown_seconds, 300); // check again later
					}
				}

				if(enterSleep)
				{
					flushSessionHistory();
					if((g_sleepType == SLEEP_FOREVER) || (g_sleepType == SLEEP_POWER_OFF_OVERRIDE))
					{
						time_t loaded_start_epoch;
						time_t loaded_finish_epoch;
						atomic_read_time_pair(&g_evteng_loaded_start_epoch, &g_evteng_loaded_finish_epoch, &loaded_start_epoch, &loaded_finish_epoch);
						if(eventScheduledForTheFuture(loaded_start_epoch, loaded_finish_epoch)) /* Never sleep forever if an event is scheduled to start in the future */
						{
							g_sleepType = SLEEP_UNTIL_START_TIME;
						}
						else
						{
							atomic_write_time(&g_time_to_wake_up, FOREVER_EPOCH);

							if(!timeIsSet())
							{
								if(!g_meshmode)
								{
									sb_send_NewLine();
									sb_send_string(TEXT_POWER_OFF);
									while((util_delay_ms(2000)) && serialbusTxInProgress())
										;
									while(util_delay_ms(200))
										; // Let serial xmsn finish before power off
								}

								if(!g_charge_battery)
								{
									PORTA_set_pin_level(POWER_ENABLE, LOW); /* No need to preserve current time, so power off - but if charging, keep power switch on to measure internal battery level */
								}
							}
							else if(!g_meshmode)
							{
								sb_send_NewLine();
								sb_send_string(TEXT_SLEEPING_TXT);
								while((util_delay_ms(2000)) && serialbusTxInProgress())
									;
								while(util_delay_ms(200))
									; // Let serial xmsn finish before sleep
							}
						}
					}

					if(!g_meshmode)
					{
						util_delay_ms(0);

						if(g_sleepType == SLEEP_UNTIL_START_TIME)
						{
							sb_send_NewLine();
							sb_send_string(TEXT_SLEEPING_UNTIL_START_TXT);
						}
						else if(g_sleepType == SLEEP_UNTIL_NEXT_XMSN)
						{
							sb_send_NewLine();
							sb_send_string(TEXT_SLEEPING_UNTIL_NEXT_XMSN);
						}

						while(util_delay_ms(300) && serialbusTxInProgress())
							; // Let serial  finish
						while(util_delay_ms(200))
							;
					}

					/* Sleeping until a scheduled start should leave the loaded event
					 * window intact so the wake-up path can resume normal scheduling.
					 */
					if((g_sleepType == SLEEP_UNTIL_START_TIME) || (g_sleepType == SLEEP_POWER_OFF_OVERRIDE))
					{
						g_evteng_run_event_until_canceled = false;
						g_evteng_event_commenced = false;
						g_foreground_start_event = false;

						time_t loaded_start_epoch;
						time_t loaded_finish_epoch;
						time_t saved_start_epoch;
						time_t saved_finish_epoch;
						atomic_read_time_pair(&g_evteng_loaded_start_epoch, &g_evteng_loaded_finish_epoch, &loaded_start_epoch, &loaded_finish_epoch);
						atomic_read_time_pair(&g_event_start_epoch, &g_event_finish_epoch, &saved_start_epoch, &saved_finish_epoch);
						if(loaded_start_epoch < MINIMUM_VALID_EPOCH) // should never be true
						{
							atomic_write_time(&g_evteng_loaded_start_epoch, saved_start_epoch);
						}

						if(loaded_finish_epoch < MINIMUM_VALID_EPOCH) // should never be true
						{
							atomic_write_time(&g_evteng_loaded_finish_epoch, saved_finish_epoch);
						}
					}

					if(g_sleepType == SLEEP_POWER_OFF_OVERRIDE)
					{
						g_sleepType = SLEEP_FOREVER;
					}

					turnCoolingFanOffForSleep();
					powerToTransmitter(OFF);
					atomic_write_u16(&g_demo_event_countdown, 0);
					g_foreground_reset_after_demo = false;
					atomic_write_u16(&g_key_down_countdown, 0);
					g_foreground_reset_after_keydown = false;

					DISABLE_INTERRUPTS();
					cancelExternalBatteryFeedback();
					LEDS.deactivate();
					serialbus_disable();
					system_sleep_config();
					clearUiButtonInjection();
					g_ignore_sleep_button_wake_until_release = rawSwitchIsClosed();
					configureSwitchInterruptForSleepWake();
					clearPendingWakeInterruptFlags();
					SLPCTRL_set_sleep_mode(SLPCTRL_SMODE_STDBY_gc);
					g_sleeping = true;
					g_awakenedBy = AWAKENED_INIT;
					ENABLE_INTERRUPTS();

					/* Standby sleep happens inside this loop until an ISR clears the
					 * foreground sleep request and records the wake source.
					 */

					while(g_go_to_sleep_now)
					{
						flushSessionHistory();
						if((g_sleepType == SLEEP_FOREVER) || (g_sleepType == SLEEP_UNTIL_START_TIME))
						{
							volatile time_t now = time(null);
							static volatile time_t hold_now = 0;

							/* Long sleeps periodically wake just enough to refresh battery
							 * measurements and charging decisions.
							 */
							if(timeDif(now, hold_now) > 90)
							{
								hold_now = now;
								system_charging_config();
								float internal_bat_voltage = readVoltage(ADCInternalBatteryVoltage); // Throw out first result following sleep
								float external_voltage = readVoltage(ADCExternalBatteryVoltage);
								atomic_write_float(&g_internal_bat_voltage, internal_bat_voltage);
								atomic_write_float(&g_external_voltage, external_voltage);
								float internal_voltage_low_threshold = atomic_read_float(&g_internal_voltage_low_threshold);
								system_sleep_config();
								setExtBatLoadSwitch(RE_APPLY_LS_STATE); // Undo any charging configuration changes to the LS setting

								if(g_enable_external_battery_control) // Control of an external battery is enabled
								{
									if(internal_bat_voltage > INT_BAT_PRESENT_VOLTAGE) // An internal battery is present
									{
										if(internal_bat_voltage < internal_voltage_low_threshold) // An external voltage is present and an internal battery is present & not fully charged
										{
											g_charge_battery = true;
										}
										else if(internal_bat_voltage >= INT_BAT_CHARGE_THRES_HIGH)
										{
											g_charge_battery = false;

											if(now < MINIMUM_VALID_EPOCH)
											{
												PORTA_set_pin_level(POWER_ENABLE, LOW); /* No need to preserve current time, so power off */
											}
										}
									}
								}
								else
								{
									g_charge_battery = false;

									if(now < MINIMUM_VALID_EPOCH)
									{
										PORTA_set_pin_level(POWER_ENABLE, LOW); /* No need to preserve current time, so power off */
									}
								}
							}
						}

						if(g_enable_external_battery_control)
							setExtBatLoadSwitch(g_charge_battery, INTERNAL_BATTERY_CHARGING);

						set_sleep_mode(SLEEP_MODE_STANDBY);
						//					set_sleep_mode(SLEEP_MODE_PWR_DOWN);
						DISABLE_INTERRUPTS();
						configureSwitchInterruptForSleepWake();
						clearPendingWakeInterruptFlags();
						sleep_enable();
						ENABLE_INTERRUPTS();
						sleep_cpu(); /* Sleep occurs here */
						sleep_disable();
					}

					if(g_awakenedBy == AWAKENED_BY_BUTTONPRESS)
					{
						setWakeAuthorizationLedPinsOn();
					}

					CLKCTRL_init();
					/* Re-run the normal startup helpers after standby wake so the
					 * peripheral drivers and GPIO configuration are back in the
					 * awake-state configuration expected by the foreground loop.
					 * Keep the RTC running in-place so standby wake does not
					 * re-phase the 1 Hz tick and introduce accumulated clock slip.
					 */
					g_sleeping = false;
					atomic_write_time(&g_seconds_since_wakeup, 0);
					g_temperature_fresh_seconds = 0;
					system_resume_from_standby();
					sampleTemperatureNow();
					g_restart_conversions = true;
					configureSwitchInterruptForAwake();
					if(!sb_enabled())
						serialbus_init(SB_BAUD, SERIALBUS_USART);

					if(g_enable_external_battery_control)
						setExtBatLoadSwitch(g_charge_battery, INTERNAL_BATTERY_CHARGING);

					if(g_awakenedBy == AWAKENED_BY_BUTTONPRESS)
					{
						g_device_wakeup_complete = false;                // Set the flag to ignore key presses other than an initial long press
						g_foreground_check_for_long_wakeup_press = true; // Set the flag to check for an initial long keypress before waking up the device
						LEDS.init();
						LEDS.setWakeAuthorizationBlink(true);
						buttonHeldClosed = true;
						while(util_delay_ms(2000))
							;
					}

					atomic_write_u16(&g_evteng_sleepshutdown_seconds, 300);

					/* A button wake must earn authorization again before the unit is
					 * allowed to remain fully awake.
					 */
					if(g_awakenedBy == AWAKENED_BY_BUTTONPRESS)
					{
						atomic_write_u16(&g_button_hold_countdown, WAKE_AUTH_HOLD_TICKS);
						atomic_write_u16(&g_foreground_handle_counted_presses, 0);

						if((g_button_wake_prior_sleep_type == SLEEP_UNTIL_START_TIME) || (g_button_wake_prior_sleep_type == SLEEP_UNTIL_NEXT_XMSN)) /* User woke up the transmitter early, before transmissions were to start */
						{
							g_foreground_start_event = false;
							if(g_button_wake_prior_sleep_type == SLEEP_UNTIL_START_TIME)
							{
								g_evteng_event_commenced = false;
							}
						}
					}
					/* Serial-port wake resumes the user interface immediately without
					 * the long-hold authorization step used for button wakes.
					 */
					else if(g_awakenedBy == AWAKENED_BY_SERIAL_PORT)
					{
						LEDS.init();
						atomic_max_u16(&g_evteng_sleepshutdown_seconds, 300U);
						if(!g_cloningInProgress && !g_meshmode)
						{
							configRedLEDforEvent();
							LEDS.blink(LEDS_GREEN_ON_CONSTANT);
							atomic_write_u16(&g_report_settings_countdown, 100);
						}
					}
					/* Clock wake resumes the pending event window or transitions into
					 * the event's active phase, depending on the prior sleep mode.
					 */
					else
					{
						if(g_sleepType == SLEEP_UNTIL_NEXT_XMSN)
						{
							g_sleepType = SLEEP_AFTER_EVENT;
						}
						else
						{
							if(!currentLoadedEventWindowCanceled())
							{
								g_foreground_start_event = true;
							}
						}
					}
					if(g_awakenedBy != AWAKENED_BY_BUTTONPRESS)
					{
						serialbus_set_rx_accepting_input(true);
					}

					/* Restore the transmitter power state that matches the logical
					 * wake state we just transitioned into.
					 */
					bool should_power_tx = shouldPowerTransmitterAfterWake();
					if(!powerToTransmitter(should_power_tx))
					{
						if(should_power_tx)
						{
							sb_send_string(TEXT_TX_NOT_RESPONDING_TXT);
						}
					}
				}
			}
			else
			{
				g_device_wakeup_complete = true; // Set the flag to accept user key presses
			}

			if(g_pending_led_revival)
			{
				g_pending_led_revival = false;
				reviveLedActivityForCurrentState();
				atomic_max_u16(&g_evteng_sleepshutdown_seconds, 300U);
			}

			if(g_foreground_exit_calibration)
			{
				g_foreground_exit_calibration = false;
				atomic_write_u16(&g_foreground_handle_counted_presses, 0);
				g_long_button_press = false;
				if(txCalibrationCarrierActive())
				{
					if(txExitCalibrationCarrier())
						sb_send_string(TEXT_TX_NOT_RESPONDING_TXT);
					else
						sb_send_string((char *)"* RF calibration carrier exited by button\n");
				}
			}

			uint16_t counted_presses = atomic_exchange_u16(&g_foreground_handle_counted_presses, 0);
			if(counted_presses)
			{
				bool release_deferred_clone_start = false;
				if(atomic_read_u16(&g_send_clone_success_countdown) || g_cloningInProgress)
				{
					release_deferred_clone_start = atomic_read_u16(&g_send_clone_success_countdown) && g_defer_cloned_event_start;
					atomic_write_u16(&g_send_clone_success_countdown, 0);
					g_cloningInProgress = false;
					atomic_write_u16(&g_programming_msg_throttle, 0);
					resumeLoadedEventAfterCloneExit(false);
					counted_presses = 0; /* Throw out any keypresses that occurred while cloning or sending cloning success pattern */
				}

				if(release_deferred_clone_start)
				{
					g_defer_cloned_event_start = false;
					g_foreground_start_event = true;
				}

				if(g_isMaster)
				{
					if(counted_presses == 5)
					{
						if(atomic_read_u16(&g_key_down_countdown))
						{
							atomic_write_u16(&g_key_down_countdown, 0);
							LEDS.setRed(OFF);
							keyTransmitter(OFF);
							powerToTransmitter(OFF);
						}

						if(atomic_read_u16(&g_demo_event_countdown))
						{
							atomic_write_u16(&g_demo_event_countdown, 0);
							LEDS.setRed(OFF);
							keyTransmitter(OFF);
							powerToTransmitter(OFF);
						}

						atomic_write_u16(&isMasterCountdownSeconds, 0);
						sb_send_NewPrompt();
						g_isMaster = false;
						atomic_write_u16(&g_evteng_sleepshutdown_seconds, 300); /* Resume normal slave sleep timeout */
						g_evteng_event_commenced = false;
						g_defer_cloned_event_start = false;
						g_foreground_start_event = loadedEventShouldBeEnabled();
						g_cloningInProgress = false;
						atomic_write_u16(&g_programming_countdown, 0);
						atomic_write_u16(&g_programming_msg_throttle, 0);
						atomic_write_u16(&g_send_clone_success_countdown, 0);
						LEDS.init();
						text_buff_reset_atomic();
					}
					else if(counted_presses == 9) // Perform software reset
					{
						RSTCTRL_reset();
					}
				}
				else // not Master
				{
					if(counted_presses == 1)
					{
						if(!g_cloningInProgress && g_device_enabled)
						{
							if(g_event_canceled_by_user)
							{
								startEvent();
							}
							else if(getFoxSetting() == FREQUENCY_TEST_BEACON)
							{
								atomic_write_u16(&g_evteng_sleepshutdown_seconds, 300);
								if(!txIsInitialized())
								{
									if(!powerToTransmitter(g_device_enabled))
									{
										sb_send_string(TEXT_TX_NOT_RESPONDING_TXT);
									}
								}

								g_evteng_code_throttle = throttleValue(getFoxCodeSpeed());

								if(++g_frequency_to_test >= NUMBER_OF_TEST_FREQUENCIES)
									g_frequency_to_test = 0;

								if(g_frequency_to_test == 0)
								{
									txSetFrequency(&g_frequency_low, true);
								}
								else if(g_frequency_to_test == 1)
								{
									txSetFrequency(&g_frequency_med, true);
								}
								else if(g_frequency_to_test == 2)
								{
									txSetFrequency(&g_frequency_hi, true);
								}
								else if(g_frequency_to_test == 3)
								{
									txSetFrequency(&g_frequency_beacon, true);
								}

								setupForFox(USE_CURRENT_FOX, START_TRANSMISSIONS_NOW);
							}
							else
							{
								time_t loaded_start_epoch;
								time_t loaded_finish_epoch;
								bool current_window_running;
								bool future_window_only;

								g_start_event_after_keydown = false;
								atomic_read_time_pair(&g_evteng_loaded_start_epoch, &g_evteng_loaded_finish_epoch, &loaded_start_epoch, &loaded_finish_epoch);
								current_window_running = eventIsScheduledToRunNow(loaded_start_epoch, loaded_finish_epoch);
								future_window_only = eventScheduledForTheFuture(loaded_start_epoch, loaded_finish_epoch);

								if(current_window_running)
								{
									bool had_demo_countdown = atomic_read_u16(&g_demo_event_countdown);
									bool had_keydown_countdown = atomic_read_u16(&g_key_down_countdown);
									suspendEvent();

									if(had_demo_countdown)
									{
										atomic_write_u16(&g_demo_event_countdown, 0);
										g_foreground_reset_after_demo = false;
									}

									if(had_keydown_countdown)
									{
										atomic_write_u16(&g_key_down_countdown, 0);
										g_foreground_reset_after_keydown = false;
										g_event_launched_by_user_action = false;
										LEDS.init();
										startEventUsingRTC();
									}
									else if(had_demo_countdown)
									{
										g_event_launched_by_user_action = false;
										LEDS.init();
										startEventUsingRTC();
									}
									else
									{
#ifdef TEST_MODE_SOFTWARE
										atomic_write_u16(&g_key_down_countdown, 36000); // 120 seconds
#else
										atomic_write_u16(&g_key_down_countdown, 9000); // 30 seconds
#endif
										g_event_launched_by_user_action = false;
										if(syncCurrentFrequencySetting(true))
										{
											sb_send_string(TEXT_TX_NOT_RESPONDING_TXT);
										}
										if(!powerToTransmitter(g_device_enabled))
										{
											sb_send_string(TEXT_TX_NOT_RESPONDING_TXT);
										}
										LEDS.init();
										LEDS.setRed(ON);
										keyTransmitter(ON);
										g_evteng_event_enabled = false;
										g_evteng_run_event_until_canceled = true;
									}

									atomic_write_u16(&g_evteng_sleepshutdown_seconds, 300);
								}
								else if(future_window_only)
								{
									/* Implement special behavior if an event is scheduled to commence in the future: have a single button press toggle between
									 * transmitting and slow blinking. But, in either case, the transmitter should eventually go to sleep and awaken at the
									 * appointed time for the future event */
									uint8_t inc = 0;
									if(atomic_read_u16(&g_key_down_countdown))
									{
										atomic_write_u16(&g_key_down_countdown, 0);
										g_foreground_reset_after_keydown = false;
										inc = 1;
									}

									if(atomic_read_u16(&g_demo_event_countdown))
									{
										atomic_write_u16(&g_demo_event_countdown, 0);
										g_foreground_reset_after_demo = false;
										inc = 2;
									}

									switch(inc)
									{
										case 0: /* 30 second keydown */
										{
											suspendEvent();
#ifdef TEST_MODE_SOFTWARE
											atomic_write_u16(&g_key_down_countdown, 36000); // 120 seconds
#else
											atomic_write_u16(&g_key_down_countdown, 9000); // 30 seconds
#endif
											if(syncCurrentFrequencySetting(true))
											{
												sb_send_string(TEXT_TX_NOT_RESPONDING_TXT);
											}
											if(!powerToTransmitter(g_device_enabled))
											{
												sb_send_string(TEXT_TX_NOT_RESPONDING_TXT);
											}
											LEDS.init();
											LEDS.setRed(ON);
											keyTransmitter(ON);
											g_evteng_event_enabled = false; // Keydown is not controlled by the Event Engine
											g_evteng_run_event_until_canceled = true;
											g_start_event_after_keydown = true;
										}
										break;

										case 1: /* 30 second demo transmission */
										{
											suspendEvent();

											if(g_evteng_on_air_seconds < 30)
											{
												atomic_write_u16(&g_demo_event_countdown, g_evteng_on_air_seconds * 300); // transmit seconds
											}
											else
											{
												atomic_write_u16(&g_demo_event_countdown, 9000); // 30 seconds
											}

											if(syncCurrentFrequencySetting(true))
											{
												sb_send_string(TEXT_TX_NOT_RESPONDING_TXT);
											}
											if(!powerToTransmitter(g_device_enabled))
											{
												sb_send_string(TEXT_TX_NOT_RESPONDING_TXT);
											}

											LEDS.init();
											startTransmissionsNow(true);
										}
										break;

										default: //	case 2: Start the event normally
										{
											startEvent();
										}
										break;
									}

									atomic_write_u16(&g_evteng_sleepshutdown_seconds, 300); // Sleep after 5 minutes
								}
								else // No event scheduled for the future (one might be in progress, or none is scheduled at all)
								{
									suspendEvent();

									if(atomic_read_u16(&g_demo_event_countdown))
									{
										atomic_write_u16(&g_demo_event_countdown, 0);
										g_foreground_reset_after_demo = false;
										// Restore the currently relevant saved event window.
										reloadLoadedEventWindowFromSavedSettings();
									}

									if(atomic_read_u16(&g_key_down_countdown))
									{
										atomic_write_u16(&g_key_down_countdown, 0); // Cancel countdown
										g_foreground_reset_after_keydown = false;
										g_event_launched_by_user_action = true;
										LEDS.init();
#ifndef TEST_MODE_SOFTWARE
										startSyncdEventNow(true); // Immediately start the event (sync to the clock if possible)
#endif
									}
									else
									{
#ifdef TEST_MODE_SOFTWARE
										atomic_write_u16(&g_key_down_countdown, 36000); // 120 seconds
#else
										atomic_write_u16(&g_key_down_countdown, 9000); // 30 seconds
#endif
										g_start_event_after_keydown = true;
										if(syncCurrentFrequencySetting(true))
										{
											sb_send_string(TEXT_TX_NOT_RESPONDING_TXT);
										}
										if(!powerToTransmitter(g_device_enabled))
										{
											sb_send_string(TEXT_TX_NOT_RESPONDING_TXT);
										}
										LEDS.init();
										LEDS.setRed(ON);
										keyTransmitter(ON);
										g_evteng_event_enabled = false;
										g_evteng_run_event_until_canceled = true;
									}
								}
							}
						}
					}
					else if(counted_presses == 3)
					{
						cancelEventFromButton();
					}
					else if(counted_presses == 5)
					{
						bool had_transient_state = g_start_event_after_keydown || atomic_read_u16(&g_key_down_countdown) || atomic_read_u16(&g_demo_event_countdown) || g_foreground_reset_after_keydown || g_foreground_reset_after_demo;
						if(had_transient_state)
						{
							cancelManualTransientState();
							suspendEvent();
						}

						g_isMaster = true;
						g_evteng_event_commenced = false;
						atomic_write_u16(&isMasterCountdownSeconds, 600);       /* Remain Master for 10 minutes */
						atomic_write_u16(&g_evteng_sleepshutdown_seconds, 720); /* Never sleep while master; slave timeout starts after master ends */

						g_cloningInProgress = false;
						atomic_write_u16(&g_programming_countdown, 0);
						atomic_write_u16(&g_send_clone_success_countdown, 0);
						LEDS.init();
						text_buff_reset_atomic();
					}
					else if(counted_presses == 7)
					{
						if(!g_device_enabled)
						{
							g_device_enabled = true;
							g_ee_mgr.updateEEPROMVar(Device_Enabled, (void *)&g_device_enabled);
							time_t now = time(null);
							now++;
							while(now >= time(null))
								;
							RSTCTRL_reset();
						}
					}
				}
			}

			if(g_foreground_start_event) // This flag instructs the foreground to "launch" the event by first configuring the interrupt settings based on user-set event settings
			{
				g_foreground_start_event = false;

				if(!g_isMaster)
				{
					// Here, we have the foreground loop launch whatever event is already loaded into the Event Engine

					g_evteng_run_event_until_canceled = false;   // Foreground auto-start is only used for scheduled event launches
					setupForFox(USE_CURRENT_FOX, START_NOTHING); // Refresh fox-specific timing before launching a loaded event
					reinitializeEventEngine();

					LEDS.init();
					if(!launchLoadedEvent())
					{
						sb_send_string((char *)"* Err: event not launched\n");
					}

					LEDS.init();
					atomic_write_u16(&g_evteng_sleepshutdown_seconds, 300);
				}
			}

			if(g_foreground_enable_transmitter) // This flag to the foreground allows the transmitter to be turned on using I2C by interrupts
			{
				g_foreground_enable_transmitter = false;
				if(!powerToTransmitter(g_device_enabled))
				{
					sb_send_string(TEXT_TX_NOT_RESPONDING_TXT);
				}
			}

			if(g_foreground_report_settings)
			{
				g_foreground_report_settings = false;
				reportSettings();
				sb_send_NewLine();
				sb_send_NewPrompt();
			}

			if(g_isMaster)
			{
				handleSerialCloning();

				if(text_buff_empty_atomic())
				{
					if(!atomic_read_u16(&g_key_down_countdown) && !atomic_read_u16(&g_demo_event_countdown))
					{
						if(atomic_read_u16(&g_send_clone_success_countdown))
						{
							LEDS.sendCode((char *)"X ");
						}
						else
						{
							LEDS.sendCode((char *)"M ");
						}
					}
				}
				else /* Make sure the text buffer is being emptied */
				{
					g_enable_manual_transmissions = true; /* There is only one consumer of g_text_buff so it is always OK to enable manual transmissions */
				}

				if(!atomic_read_u16(&isMasterCountdownSeconds))
				{
					g_isMaster = false;
					atomic_write_u16(&g_evteng_sleepshutdown_seconds, 300); /* Ensure sleep occurs */
					atomic_write_u16(&g_send_clone_success_countdown, 0);
					g_foreground_start_event = loadedEventShouldBeEnabled(); /* Start any event stored in EEPROM */
					LEDS.init();
				}
			}
			else
			{
				handleSerialBusMsgs();

				if(g_defer_cloned_event_start && !g_cloningInProgress && !atomic_read_u16(&g_send_clone_success_countdown) && !g_foreground_start_event)
				{
					resumeLoadedEventAfterCloneExit(false);
				}

				if(g_cloningInProgress && !atomic_read_u16(&g_programming_countdown)) // Cloning timed out
				{
					g_cloningInProgress = false;
					resumeLoadedEventAfterCloneExit(false);
				}

				if(text_buff_empty_atomic())
				{
					time_t seconds_since_wakeup = atomic_read_time(&g_seconds_since_wakeup);
					if((seconds_since_wakeup < 60) && (g_hardware_error & ((int)HARDWARE_NO_RTC | (int)HARDWARE_NO_SI5351)))
					{
						if(g_hardware_error & ((int)HARDWARE_NO_RTC))
						{
							LEDS.sendCode((char *)"5CLK");
						}

						if(g_hardware_error & ((int)HARDWARE_NO_SI5351))
						{
							LEDS.sendCode((char *)"5XMT");
						}
					}
					else if(!g_device_enabled)
					{
						LEDS.blink(LEDS_RED_THEN_GREEN_BLINK_SLOW, true);
					}
					else if(g_cloningInProgress || atomic_read_u16(&g_key_down_countdown))
					{
						LEDS.blink(LEDS_RED_ON_CONSTANT, true);
					}
					else if(g_foreground_start_event)
					{
						time_t loaded_start_epoch;
						time_t loaded_finish_epoch;
						atomic_read_time_pair(&g_evteng_loaded_start_epoch, &g_evteng_loaded_finish_epoch, &loaded_start_epoch, &loaded_finish_epoch);

						if(eventIsScheduledToRunNow(loaded_start_epoch, loaded_finish_epoch))
						{
							LEDS.blink(LEDS_RED_OFF);
						}
						else if(eventScheduledForTheFuture(loaded_start_epoch, loaded_finish_epoch))
						{
							LEDS.blink(LEDS_RED_BLINK_SLOW);
						}
						else
						{
							LEDS.blink(LEDS_RED_BLINK_FAST);
						}
					}
					else if(!g_evteng_event_commenced)
					{
						if(atomic_read_u16(&g_send_clone_success_countdown))
						{
							LEDS.sendCode((char *)"X ");
						}
						else
						{
							time_t loaded_start_epoch;
							time_t loaded_finish_epoch;
							bool active_event_window;
							atomic_read_time_pair(&g_evteng_loaded_start_epoch, &g_evteng_loaded_finish_epoch, &loaded_start_epoch, &loaded_finish_epoch);
							active_event_window = eventIsScheduledToRunNow(loaded_start_epoch, loaded_finish_epoch) &&
							                      (g_evteng_event_enabled || g_foreground_start_event || (g_sleepType == SLEEP_AFTER_EVENT) || (g_sleepType == SLEEP_UNTIL_NEXT_XMSN));

							if(active_event_window)
							{
								LEDS.blink(LEDS_RED_OFF);
							}
							else if(noEventWillRun()) /* No event is running now, nor will one run in the future */
							{
								LEDS.blink(LEDS_RED_BLINK_FAST);
							}
							else if(eventScheduledForTheFuture(loaded_start_epoch, loaded_finish_epoch) ||
							        eventIsScheduledToRun(&g_evteng_loaded_start_epoch, &g_evteng_loaded_finish_epoch)) /* An event is scheduled to run in the future = OK */
							{
								LEDS.blink(LEDS_RED_BLINK_SLOW);
							}
							else /* Should not reach here, but if we do, it is an error */
							{
								LEDS.blink(LEDS_RED_BLINK_FAST);
							}
						}
					}
				}
				else /* Make sure the text buffer is being emptied */
				{
					g_enable_manual_transmissions = true; /* There is only one consumer of g_text_buff so it is always OK to enable manual transmissions */
				}
			}

			if(g_device_enabled)
			{
				float internal_bat_voltage = atomic_read_float(&g_internal_bat_voltage);
				float internal_voltage_low_threshold = atomic_read_float(&g_internal_voltage_low_threshold);
				float external_voltage = atomic_read_float(&g_external_voltage);
				internal_bat_error = (g_internal_bat_detected && (internal_bat_voltage <= internal_voltage_low_threshold));

				configGreenLEDForCurrentState(internal_bat_error, external_voltage);
			}
			else
			{
				LEDS.blink(LEDS_RED_THEN_GREEN_BLINK_SLOW, true);
			}

			if(g_long_button_press) /* Shut things down and go to sleep or power off */
			{
				handleLongButtonPress();
			}
		}

		if(g_foreground_reset_after_demo)
		{
			noteSessionStopped(REASON_TIMEOUT);
			atomic_write_u16(&g_demo_event_countdown, 0);
			g_foreground_reset_after_demo = false;

			suspendEvent();

			if(g_event_canceled_by_user)
			{
				/* Do not let a stale demo timeout resurrect an event the user canceled. */
			}
			else if(eventIsScheduledToRun(&g_evteng_loaded_start_epoch, &g_evteng_loaded_finish_epoch))
			{
				g_event_launched_by_user_action = false;
				startEventUsingRTC();
			}
			else
			{
				g_sleepType = SLEEP_FOREVER;
				startEventNow(true); // Immediately start the event
			}
		}

		if(g_foreground_reset_after_keydown)
		{
			noteSessionStopped(REASON_TIMEOUT);
			bool should_resume_scheduled_event = eventIsScheduledToRun(&g_evteng_loaded_start_epoch, &g_evteng_loaded_finish_epoch);

			atomic_write_u16(&g_key_down_countdown, 0);
			g_foreground_reset_after_keydown = false;

			suspendEvent();

			g_frequency_to_test = NUMBER_OF_TEST_FREQUENCIES;
			if(g_event_canceled_by_user)
			{
				g_start_event_after_keydown = false;
			}

#ifndef TEST_MODE_SOFTWARE
			if(!g_event_canceled_by_user && should_resume_scheduled_event)
			{
				g_event_launched_by_user_action = false;
				startEventUsingRTC();
			}
			else if(!g_event_canceled_by_user && g_start_event_after_keydown) // indicates that a keypress was used to initiate the keydown when no event was scheduled
			{
				g_sleepType = SLEEP_FOREVER;
				startSyncdEventNow(true); // Immediately start the event, synchronized to the clock if possible
			}
#endif

			g_start_event_after_keydown = false;
		}
	}
}

/***********************************************************************
 * Support Functions
 ************************************************************************/

/* Event engine state and scheduling helpers. */

/**
 * Clear any temporary manual-start or demo state and report whether a start was pending.
 *
 * This helper resets transient foreground-only launch state that should not
 * survive a clock change, clone exit, or similar control-flow reset.
 *
 * @return true if a one-shot start-after-keydown request had been pending.
 */
static bool cancelManualTransientState(void)
{
	bool pending_start_after_keydown = g_start_event_after_keydown;
	bool had_transient_state = pending_start_after_keydown || atomic_read_u16(&g_key_down_countdown) || g_foreground_reset_after_keydown || atomic_read_u16(&g_demo_event_countdown) || g_foreground_reset_after_demo;

	if(had_transient_state)
	{
		atomic_write_u16(&g_key_down_countdown, 0);
		atomic_write_u16(&g_demo_event_countdown, 0);
		g_foreground_reset_after_keydown = false;
		g_foreground_reset_after_demo = false;
		g_start_event_after_keydown = false;
		g_frequency_to_test = NUMBER_OF_TEST_FREQUENCIES;
	}

	return pending_start_after_keydown;
}

/**
 * Snapshot the event window that should be restored when serial cloning exits.
 *
 * The snapshot normally mirrors the saved event window, but if a shifted loaded
 * window is already active it preserves that currently relevant day instead.
 */
static void captureCloneTimingSnapshot(void)
{
	time_t saved_start_epoch;
	time_t saved_finish_epoch;
	time_t loaded_start_epoch;
	time_t loaded_finish_epoch;
	uint8_t total_days = g_days_to_run;
	uint8_t completed_days = g_schedule_day_index;
	uint8_t days_remaining = (completed_days < total_days) ? (total_days - completed_days) : 1;

	atomic_read_time_pair(&g_event_start_epoch, &g_event_finish_epoch, &saved_start_epoch, &saved_finish_epoch);
	atomic_read_time_pair(&g_evteng_loaded_start_epoch, &g_evteng_loaded_finish_epoch, &loaded_start_epoch, &loaded_finish_epoch);

	g_clone_timing_snapshot.event_start_epoch = saved_start_epoch;
	g_clone_timing_snapshot.event_finish_epoch = saved_finish_epoch;
	g_clone_timing_snapshot.days_to_run = total_days ? total_days : 1;

	bool loaded_window_is_active = eventScheduledForTheFuture(loaded_start_epoch, loaded_finish_epoch) || eventIsScheduledToRunNow(loaded_start_epoch, loaded_finish_epoch);
	bool loaded_window_differs_from_saved = (loaded_start_epoch != saved_start_epoch) || (loaded_finish_epoch != saved_finish_epoch);

	if(loaded_window_is_active && loaded_window_differs_from_saved)
	{
		g_clone_timing_snapshot.event_start_epoch = loaded_start_epoch;
		g_clone_timing_snapshot.event_finish_epoch = loaded_finish_epoch;
		g_clone_timing_snapshot.days_to_run = days_remaining ? days_remaining : 1;
	}
}

/**
 * Ask the event engine to rebuild its internal state from the current globals.
 *
 * The helper sets the foreground-to-ISR initialization flag, then waits until
 * the event engine clears it after rebuilding its runtime state.
 */
static void reinitializeEventEngine(void)
{
	g_evteng_initialize_event = true;
	util_delay_ms(0);
	while(util_delay_ms(17) && g_evteng_initialize_event)
		; // Wait for event engine to initialize
}

/**
 * Load event timing parameters that correspond to the selected fox or beacon role.
 *
 * The chosen fox determines the intra-cycle offset and the on-air/off-air/ID
 * cadence that the event engine should use for the current event family.
 *
 * @param fox Fox or beacon role whose timing profile should be applied. Passing
 *            USE_CURRENT_FOX causes the current event selection to be used.
 */
static void loadEventTimingForFox(Fox_t fox)
{
	bool delayNotSet = true;

	if(fox == USE_CURRENT_FOX)
	{
		fox = getFoxSetting();
	}

	switch(fox)
	{
		case FOX_1:
		{
			delayNotSet = false;
			g_evteng_intra_cycle_delay_time = 0;
		}
		case FOX_2:
		{
			if(delayNotSet)
			{
				delayNotSet = false;
				g_evteng_intra_cycle_delay_time = 60;
			}
		}
		case FOX_3:
		{
			if(delayNotSet)
			{
				delayNotSet = false;
				g_evteng_intra_cycle_delay_time = 120;
			}
		}
		case FOX_4:
		{
			if(delayNotSet)
			{
				delayNotSet = false;
				g_evteng_intra_cycle_delay_time = 180;
			}
		}
		case FOX_5:
		{
			if(delayNotSet)
			{
				g_evteng_intra_cycle_delay_time = 240;
			}

			g_evteng_ID_period_seconds = 60;
			atomic_write_int(&g_evteng_sendID_seconds_countdown, g_evteng_ID_period_seconds);
			g_evteng_on_air_seconds = 60;
			g_evteng_off_air_seconds = 240;
		}
		break;

		case SPRINT_S1:
		{
			if(delayNotSet)
			{
				delayNotSet = false;
				g_evteng_intra_cycle_delay_time = 0;
			}
		}
		case SPRINT_S2:
		{
			if(delayNotSet)
			{
				delayNotSet = false;
				g_evteng_intra_cycle_delay_time = 12;
			}
		}
		case SPRINT_S3:
		{
			if(delayNotSet)
			{
				delayNotSet = false;
				g_evteng_intra_cycle_delay_time = 24;
			}
		}
		case SPRINT_S4:
		{
			if(delayNotSet)
			{
				delayNotSet = false;
				g_evteng_intra_cycle_delay_time = 36;
			}
		}
		case SPRINT_S5:
		{
			if(delayNotSet)
			{
				g_evteng_intra_cycle_delay_time = 48;
			}

			g_evteng_ID_period_seconds = 600;
			atomic_write_int(&g_evteng_sendID_seconds_countdown, 600);
			g_evteng_on_air_seconds = 12;
			g_evteng_off_air_seconds = 48;
		}
		break;

		case SPRINT_F1:
		{
			delayNotSet = false;
			g_evteng_intra_cycle_delay_time = 0;
		}
		case SPRINT_F2:
		{
			if(delayNotSet)
			{
				delayNotSet = false;
				g_evteng_intra_cycle_delay_time = 12;
			}
		}
		case SPRINT_F3:
		{
			if(delayNotSet)
			{
				delayNotSet = false;
				g_evteng_intra_cycle_delay_time = 24;
			}
		}
		case SPRINT_F4:
		{
			if(delayNotSet)
			{
				delayNotSet = false;
				g_evteng_intra_cycle_delay_time = 36;
			}
		}
		case SPRINT_F5:
		{
			if(delayNotSet)
			{
				g_evteng_intra_cycle_delay_time = 48;
			}

			g_evteng_ID_period_seconds = 600;
			atomic_write_int(&g_evteng_sendID_seconds_countdown, g_evteng_ID_period_seconds);
			g_evteng_on_air_seconds = 12;
			g_evteng_off_air_seconds = 48;
		}
		break;

#if SUPPORT_TEMP_AND_VOLTAGE_REPORTING
		case REPORT_BATTERY:
		{
			g_evteng_intra_cycle_delay_time = 0;
		}
		break;
#endif // SUPPORT_TEMP_AND_VOLTAGE_REPORTING

		case FOXORING_FOX1:
		case FOXORING_FOX2:
		case FOXORING_FOX3:
		{
			g_evteng_intra_cycle_delay_time = 0;
			g_evteng_ID_period_seconds = 600;
			atomic_write_int(&g_evteng_sendID_seconds_countdown, g_evteng_ID_period_seconds);
			g_evteng_on_air_seconds = 600;
			g_evteng_off_air_seconds = 0;
		}
		break;

		case FREQUENCY_TEST_BEACON:
		{
			g_evteng_intra_cycle_delay_time = 0;
			g_evteng_ID_period_seconds = 600;
			atomic_write_int(&g_evteng_sendID_seconds_countdown, g_evteng_ID_period_seconds);
			g_evteng_on_air_seconds = 600;
			g_evteng_off_air_seconds = 0;
			atomic_write_u16(&g_evteng_sleepshutdown_seconds, 300);
		}
		break;

		case SPECTATOR:
		case BEACON:
		default:
		{
			g_evteng_intra_cycle_delay_time = 0;
			g_evteng_ID_period_seconds = 600;
			atomic_write_int(&g_evteng_sendID_seconds_countdown, g_evteng_ID_period_seconds);
			g_evteng_on_air_seconds = 600;
			g_evteng_off_air_seconds = 0;
		}
		break;
	}
}

/**
 * Restore the loaded event after cloning, optionally deferring the restart.
 *
 * @param deferStartIfAlreadyRunning true to defer the restart when the restored
 *                                   window is already active at clone exit.
 */
static void resumeLoadedEventAfterCloneExit(bool deferStartIfAlreadyRunning)
{
	bool should_resume_loaded_event = loadedEventShouldBeEnabled();
	time_t loaded_start_epoch;
	time_t loaded_finish_epoch;

	atomic_read_time_pair(&g_evteng_loaded_start_epoch, &g_evteng_loaded_finish_epoch, &loaded_start_epoch, &loaded_finish_epoch);

	if(deferStartIfAlreadyRunning && should_resume_loaded_event && eventIsScheduledToRunNow(loaded_start_epoch, loaded_finish_epoch))
	{
		g_defer_cloned_event_start = true;
		g_foreground_start_event = false;
	}
	else
	{
		g_defer_cloned_event_start = false;
		g_foreground_start_event = should_resume_loaded_event;
	}
}

/**
 * Rebuild the currently loaded event window from saved settings and day counters.
 *
 * The helper advances the saved start/finish pair to the day that should be
 * active now, publishes the loaded window, and reports whether it is schedulable.
 *
 * @return true if the rebuilt loaded window is in the future or currently active.
 */
static bool reloadLoadedEventWindowFromSavedSettings(void)
{
	time_t saved_start_epoch;
	time_t saved_finish_epoch;
	time_t loaded_start_epoch;
	time_t loaded_finish_epoch;

	atomic_read_time_pair(&g_event_start_epoch, &g_event_finish_epoch, &saved_start_epoch, &saved_finish_epoch);

	if((g_days_to_run > 0) && (g_schedule_day_index >= g_days_to_run))
	{
		atomic_write_time_pair(&g_evteng_loaded_start_epoch, &g_evteng_loaded_finish_epoch, 0, 0);
		return false;
	}

	loaded_start_epoch = saved_start_epoch;
	loaded_finish_epoch = saved_finish_epoch;

	if((saved_start_epoch <= MINIMUM_VALID_EPOCH) || (saved_finish_epoch <= saved_start_epoch))
	{
		atomic_write_time_pair(&g_evteng_loaded_start_epoch, &g_evteng_loaded_finish_epoch, loaded_start_epoch, loaded_finish_epoch);
		return false;
	}

	uint8_t day_index = MIN(g_schedule_day_index, (uint8_t)((g_days_to_run > 0) ? (g_days_to_run - 1) : 0));
	loaded_start_epoch += ((time_t)day_index * SECONDS_24H);
	loaded_finish_epoch += ((time_t)day_index * SECONDS_24H);

	if(timeIsSet())
	{
		time_t now = time(null);
		while((loaded_finish_epoch <= now) && ((day_index + 1) < g_days_to_run))
		{
			day_index++;
			loaded_start_epoch += SECONDS_24H;
			loaded_finish_epoch += SECONDS_24H;
		}
	}

	if(timeIsSet() && loaded_finish_epoch <= time(null)) day_index = g_days_to_run;
	g_schedule_day_index = day_index;
	if(day_index >= g_days_to_run) loaded_start_epoch = loaded_finish_epoch = 0;
	atomic_write_time_pair(&g_evteng_loaded_start_epoch, &g_evteng_loaded_finish_epoch, loaded_start_epoch, loaded_finish_epoch);

	return eventScheduledForTheFuture(loaded_start_epoch, loaded_finish_epoch) || eventIsScheduledToRunNow(loaded_start_epoch, loaded_finish_epoch);
}

/**
 * Recompute the loaded event window after the system clock changes.
 *
 * A clock update can move the firmware onto a different day of a multi-day
 * schedule, so this helper recomputes the loaded window and adjusts cancel
 * state when that happens.
 *
 * @return true if a loaded event window remains schedulable after the resync.
 */
static bool resyncLoadedEventWindowAfterClockSet(void)
{
	noteSessionStopped(REASON_CLOCK);
	g_thermal_start_pending = false;
	time_t saved_start_epoch;
	time_t saved_finish_epoch;
	time_t prior_loaded_start_epoch;
	time_t prior_loaded_finish_epoch;
	uint8_t total_days = g_days_to_run ? g_days_to_run : 1;

	atomic_read_time_pair(&g_event_start_epoch, &g_event_finish_epoch, &saved_start_epoch, &saved_finish_epoch);
	atomic_read_time_pair(&g_evteng_loaded_start_epoch, &g_evteng_loaded_finish_epoch, &prior_loaded_start_epoch, &prior_loaded_finish_epoch);

	if((saved_start_epoch <= MINIMUM_VALID_EPOCH) || (saved_finish_epoch <= saved_start_epoch))
	{
		return reloadLoadedEventWindowFromSavedSettings();
	}

	uint8_t day_index = 0;
	time_t loaded_start_epoch = saved_start_epoch;
	time_t loaded_finish_epoch = saved_finish_epoch;
	time_t now = time(null);
	bool have_schedulable_window = false;

	while((loaded_finish_epoch <= now) && ((day_index + 1) < total_days))
	{
		day_index++;
		loaded_start_epoch += SECONDS_24H;
		loaded_finish_epoch += SECONDS_24H;
	}

	if(loaded_finish_epoch <= now)
	{
		day_index = total_days;
		loaded_start_epoch = 0;
		loaded_finish_epoch = 0;
	}
	else
	{
		have_schedulable_window = eventScheduledForTheFuture(loaded_start_epoch, loaded_finish_epoch) ||
		                          eventIsScheduledToRunNow(loaded_start_epoch, loaded_finish_epoch);
	}

	g_schedule_day_index = day_index;
	atomic_write_time_pair(&g_evteng_loaded_start_epoch, &g_evteng_loaded_finish_epoch, loaded_start_epoch, loaded_finish_epoch);

	/* A clock change can move us onto a different day's window. Only preserve the cancel
	 * latch if the resync kept us on the same loaded window and that window is still
	 * current. */
	if((prior_loaded_start_epoch != loaded_start_epoch) || (prior_loaded_finish_epoch != loaded_finish_epoch) ||
	   !eventIsScheduledToRunNow(loaded_start_epoch, loaded_finish_epoch))
	{
		g_event_canceled_by_user = false;
	}

	return have_schedulable_window;
}

/**
 * Advance the loaded event window to the next day after canceling today's run.
 *
 * @return true if a later day exists and the loaded window was advanced.
 */
static bool advanceLoadedEventWindowAfterCurrentDayCancel(void)
{
	reloadLoadedEventWindowFromSavedSettings();
	if((g_days_to_run <= 1) || ((g_schedule_day_index + 1) >= g_days_to_run))
	{
		return false;
	}

	g_schedule_day_index++;
	return reloadLoadedEventWindowFromSavedSettings();
}

/**
 * Report whether the currently loaded event window is still latched as canceled.
 *
 * The cancellation latch only applies to the day that is currently loaded and
 * actively runnable.
 *
 * @return true if the current loaded window should still be treated as canceled.
 */
static bool currentLoadedEventWindowCanceled(void)
{
	if(!g_event_canceled_by_user)
	{
		return false;
	}

	if(!timeIsSet())
	{
		return false;
	}

	time_t loaded_start_epoch;
	time_t loaded_finish_epoch;
	atomic_read_time_pair(&g_evteng_loaded_start_epoch, &g_evteng_loaded_finish_epoch, &loaded_start_epoch, &loaded_finish_epoch);

	/* The latch only applies to the currently loaded event window. Once the loaded window
	 * has advanced to the future, passive wake/scheduler logic must stop treating it as
	 * canceled. */
	return eventIsScheduledToRunNow(loaded_start_epoch, loaded_finish_epoch);
}

/** Is a temporary button/serial carrier or Morse demo still pending? */
static bool manualTestInProgress(void)
{
	return g_start_event_after_keydown || atomic_read_u16(&g_key_down_countdown) ||
	    atomic_read_u16(&g_demo_event_countdown) || g_foreground_reset_after_keydown || g_foreground_reset_after_demo;
}

/** Snapshot the meaning of an awake hold at its first debounced edge. */
static uint8_t buttonHoldIntent(void)
{
	if(manualTestInProgress()) return BUTTON_HOLD_STOP_TEST;
	time_t start, finish;
	atomic_read_time_pair(&g_evteng_loaded_start_epoch, &g_evteng_loaded_finish_epoch, &start, &finish);
	return eventScheduledForTheFuture(start, finish) ? BUTTON_HOLD_SLEEP_SCHEDULE : BUTTON_HOLD_DEFAULT;
}

/** Cancel today's event, or clear a test and re-arm a future event. */
static void cancelEventFromButton(void)
{
	uint8_t prior_day = g_schedule_day_index;
	bool was_temporary = manualTestInProgress();
	bool was_manual = g_event_launched_by_user_action || g_evteng_run_event_until_canceled;
	time_t loaded_start_epoch = 0;
	time_t loaded_finish_epoch = 0;
	bool event_is_scheduled;
	bool current_window_running = false;
	bool future_window_only = false;

	cancelManualTransientState();
	g_frequency_to_test = NUMBER_OF_TEST_FREQUENCIES;
	g_event_launched_by_user_action = false;

	event_is_scheduled = eventIsScheduledToRun(&g_evteng_loaded_start_epoch, &g_evteng_loaded_finish_epoch);
	if(event_is_scheduled)
	{
		atomic_read_time_pair(&g_evteng_loaded_start_epoch, &g_evteng_loaded_finish_epoch, &loaded_start_epoch, &loaded_finish_epoch);
		current_window_running = eventIsScheduledToRunNow(loaded_start_epoch, loaded_finish_epoch);
		future_window_only = eventScheduledForTheFuture(loaded_start_epoch, loaded_finish_epoch);
	}

	suspendEvent(REASON_USER);

	if(current_window_running)
	{
		g_event_canceled_by_user = true;
		if(advanceLoadedEventWindowAfterCurrentDayCancel())
		{
			g_event_canceled_by_user = false;
			startEventUsingRTC();
		}
		atomic_write_u16(&g_evteng_sleepshutdown_seconds, 300);
	}
	else if(future_window_only) // Preserve existing future-event behavior
	{
		g_event_canceled_by_user = false;
		startEventUsingRTC();
		atomic_write_u16(&g_evteng_sleepshutdown_seconds, 300);
	}
	else
	{
		g_event_canceled_by_user = false;
	}
	noteButtonAction(current_window_running && (!was_manual || was_temporary) ? BUTTON_CANCEL_DAY :
	    (was_temporary ? BUTTON_STOP_TEST : (was_manual ? BUTTON_CANCEL_MANUAL : BUTTON_REARM_SCHEDULE)), prior_day);
}

/**
 * A hold stops only a temporary test; otherwise an active calendar event uses
 * the same cancellation as three presses. Manual-run hold behavior stays below.
 */
static bool handleScheduledButtonHold(void)
{
	uint8_t prior_day = g_schedule_day_index;
	uint8_t intent = g_long_button_hold_intent;
	g_long_button_hold_intent = BUTTON_HOLD_DEFAULT;
	bool stop_test = manualTestInProgress() || intent == BUTTON_HOLD_STOP_TEST;
	if(stop_test || intent == BUTTON_HOLD_SLEEP_SCHEDULE)
	{
		bool test_still_running = manualTestInProgress();
		cancelManualTransientState();
		suspendEvent(test_still_running ? REASON_USER : REASON_SETTINGS);
		g_event_launched_by_user_action = false;
		if(reloadLoadedEventWindowFromSavedSettings() && !currentLoadedEventWindowCanceled())
		{
			startEventUsingRTC();
			time_t start, finish;
			atomic_read_time_pair(&g_evteng_loaded_start_epoch, &g_evteng_loaded_finish_epoch, &start, &finish);
			if(g_evteng_event_enabled && eventIsScheduledToRunNow(start, finish) && !transmitterThermallyBlocked())
			{
				// Retain the restored phase, waking before the next slot. If that
				// slot is already on air, the RTC resumes it on its next tick.
				int32_t on_air = atomic_read_i32(&g_evteng_on_the_air);
				time_t delay = on_air < -10 ? (time_t)(-on_air - 10) : 1;
				atomic_write_time(&g_time_to_wake_up, time(null) + delay);
				g_sleepType = SLEEP_UNTIL_NEXT_XMSN;
			}
		}
		g_foreground_enable_transmitter = false;
		keyTransmitter(OFF);
		powerToTransmitter(OFF);
		noteButtonAction(stop_test ? BUTTON_STOP_TEST : BUTTON_SLEEP_SCHEDULE, prior_day);
		return true;
	}

	time_t start, finish;
	atomic_read_time_pair(&g_evteng_loaded_start_epoch, &g_evteng_loaded_finish_epoch, &start, &finish);
	if(!g_event_launched_by_user_action && !g_evteng_run_event_until_canceled &&
	   eventIsScheduledToRunNow(start, finish))
	{
		cancelEventFromButton();
		return true;
	}
	return false;
}

/** Handle an awake long hold after the switch detector has consumed the press. */
static void handleLongButtonPress(void)
{
	bool handled_schedule = handleScheduledButtonHold();
	if(!handled_schedule && sessionCooling()) {
		noteSessionStopped(REASON_USER);
		g_evteng_event_commenced = false;
		g_event_canceled_by_user = true;
		g_thermal_start_pending = false;
	}
	else if(!handled_schedule && atomic_read_i32(&g_evteng_on_the_air) >= 0) {
		noteSessionStopped(REASON_USER);
		g_evteng_event_enabled = false;
		g_foreground_enable_transmitter = false;
		keyTransmitter(OFF);
	}
	g_long_button_press = false;
	g_foreground_check_for_long_wakeup_press = false;
	atomic_write_u16(&g_foreground_handle_counted_presses, 0);
	LEDS.blink(LEDS_OFF);
	g_isMaster = false;
	atomic_write_u16(&isMasterCountdownSeconds, 0);
	g_defer_cloned_event_start = false;
	atomic_write_u16(&g_send_clone_success_countdown, 0);
	g_cloningInProgress = false;
	atomic_write_u16(&g_programming_countdown, 0);
	atomic_write_u16(&g_programming_msg_throttle, 0);

	if(!handled_schedule)
	{
		time_t loaded_start_epoch;
		time_t loaded_finish_epoch;
		time_t now = time(null);

		finishTimedEventIfExpired(now);
		atomic_read_time_pair(&g_evteng_loaded_start_epoch, &g_evteng_loaded_finish_epoch, &loaded_start_epoch, &loaded_finish_epoch);
		int32_t on_the_air = atomic_read_i32(&g_evteng_on_the_air);
		if(g_evteng_event_enabled && eventIsScheduledToRunNow(loaded_start_epoch, loaded_finish_epoch) && (on_the_air < 0))
		{
			int32_t timeRemaining = SECONDS_24H; // Any big number will do

			if(timeIsSet() && !g_evteng_run_event_until_canceled && (loaded_start_epoch != loaded_finish_epoch) && (now < loaded_finish_epoch))
			{
				timeRemaining = timeDif(loaded_finish_epoch, now);
			}

			/* Match the event engine's normal off-air sleep guard so we do not wake for an
			 * extra post-finish slot after the user manually puts the unit back to sleep. */
			if((g_evteng_off_air_seconds > 15) && (timeRemaining > (g_evteng_off_air_seconds + g_evteng_on_air_seconds + 15)))
			{
				time_t seconds_to_sleep = MAX((time_t)1, (time_t)(-on_the_air - 10));
				g_evteng_event_enabled = true;
				g_evteng_event_commenced = true;
				atomic_write_time(&g_time_to_wake_up, now + seconds_to_sleep);
				ENTER_CRITICAL(main_sendid_sleep_adjust);
				g_evteng_sendID_seconds_countdown = MAX(0, g_evteng_sendID_seconds_countdown - (int)seconds_to_sleep);
				EXIT_CRITICAL(main_sendid_sleep_adjust);
				g_sleepType = SLEEP_UNTIL_NEXT_XMSN;
			}
			else if((loaded_start_epoch != loaded_finish_epoch) && (timeRemaining > 0))
			{
				/* Keep tracking the scheduled finish time, but leave transmissions disabled so
				 * a later manual wake cannot resurrect a slot that no longer fully fits before
				 * the event ends. */
				g_evteng_event_enabled = false;
				g_evteng_event_commenced = true;
				atomic_write_time(&g_time_to_wake_up, FOREVER_EPOCH);
				g_sleepType = SLEEP_AFTER_EVENT;
			}
			else
			{
				g_sleepType = SLEEP_AFTER_EVENT;
			}
		}
		else if(eventScheduledForTheFuture(loaded_start_epoch, loaded_finish_epoch))
		{
			g_sleepType = SLEEP_UNTIL_START_TIME;
		}
		else if(timeIsSet())
		{
			g_sleepType = SLEEP_FOREVER;
		}
		else
		{
			suspendEvent();
		}
	}

	g_go_to_sleep_now = true;
}

/** Inspect saved calendar relevance using local copies, without changing a run. */
static bool savedScheduleCanLimitManualRun(void)
{
	time_t start, finish;
	atomic_read_time_pair(&g_event_start_epoch, &g_event_finish_epoch, &start, &finish);
	return (start > MINIMUM_VALID_EPOCH) && (finish > start) && eventIsScheduledToRun(&start, &finish);
}

/**
 * Extend the temporary master role long enough for another sync/programming session.
 */
static inline void extendMasterModeTimeout(void)
{
	atomic_write_u16(&isMasterCountdownSeconds, 600); /* Remain Master for 10 minutes */
}

/**
 * End the current timed event once its loaded finish time has passed.
 *
 * The helper shuts down the active event, updates multi-day scheduling state,
 * and schedules the next wake-up when another day remains.
 *
 * @param now Current epoch time.
 * @return true if an active timed event was finished, false otherwise.
 */
static bool finishTimedEventIfExpired(time_t now)
{
	if(!(g_evteng_event_commenced && !g_evteng_run_event_until_canceled))
	{
		return false;
	}

	time_t loaded_finish_epoch = atomic_read_time(&g_evteng_loaded_finish_epoch);
	if(!loaded_finish_epoch || (now < loaded_finish_epoch))
	{
		return false;
	}

	atomic_write_i32(&g_evteng_on_the_air, 0);
	keyTransmitter(OFF);
	g_evteng_event_enabled = false;
	g_evteng_event_commenced = false;
	LEDS.init();
	noteSessionStopped(REASON_FINISH);
	g_schedule_day_index = sessionDayIndex(g_event_start_epoch, g_event_finish_epoch, g_days_to_run, now);
	atomic_write_u16(&g_evteng_sleepshutdown_seconds, 3);

	if(g_schedule_day_index < g_days_to_run)
	{
		time_t next_start_epoch = g_event_start_epoch + (time_t)g_schedule_day_index * SECONDS_24H;
		time_t next_finish_epoch = g_event_finish_epoch + (time_t)g_schedule_day_index * SECONDS_24H;
		atomic_write_time_pair(&g_evteng_loaded_start_epoch, &g_evteng_loaded_finish_epoch, next_start_epoch, next_finish_epoch);
		atomic_write_time(&g_time_to_wake_up, next_start_epoch - 15); /* Wake shortly before the next day's event begins. */
		g_sleepType = SLEEP_UNTIL_START_TIME;
		g_go_to_sleep_now = true;
	}
	else
	{
		g_sleepType = SLEEP_FOREVER;
		atomic_write_time_pair(&g_evteng_loaded_start_epoch, &g_evteng_loaded_finish_epoch, 0, 0);
	}

	return true;
}

/* Morse generation and clock-setting helpers. */

/**
 * Load the currently active automated pattern into the Morse generator safely.
 *
 * Shared pattern text is copied into a local snapshot first so the Morse
 * generator sees stable text even if other code updates the shared message slots.
 *
 * @param repeat Output flag controlling Morse repeat behavior.
 * @param caller Caller identifier forwarded to the Morse module.
 */
static void loadCurrentPatternMorse(bool *repeat, callerID_t caller)
{
	static char pattern_snapshot[MAX_PATTERN_TEXT_LENGTH + 2];
	char *pattern = getCurrentPatternText();
	if((pattern == g_messages_text[PATTERN_TEXT]) || (pattern == g_messages_text[FOXORING_PATTERN_TEXT]))
	{
		uint8_t slot = (pattern == g_messages_text[PATTERN_TEXT]) ? PATTERN_TEXT : FOXORING_PATTERN_TEXT;
		messages_text_slot_copy_atomic(slot, pattern_snapshot, sizeof(pattern_snapshot));
	}
	else
	{
		strncpy(pattern_snapshot, pattern, sizeof(pattern_snapshot) - 1);
		pattern_snapshot[sizeof(pattern_snapshot) - 1] = '\0';
	}
	makeMorse(pattern_snapshot, repeat, NULL, caller);
}

/**
 * Load the station ID text into the Morse generator using a stable snapshot.
 *
 * @param repeat Output flag controlling Morse repeat behavior.
 * @param caller Caller identifier forwarded to the Morse module.
 */
static void loadStationIDMorse(bool *repeat, callerID_t caller)
{
	static char station_id_snapshot[MAX_PATTERN_TEXT_LENGTH + 2];
	messages_text_slot_copy_atomic(STATION_ID, station_id_snapshot, sizeof(station_id_snapshot));
	makeMorse(station_id_snapshot, repeat, NULL, caller);
}

/**
 * Refresh the active automated Morse pattern when an event is running normally.
 */
static void refreshActiveAutomatedPattern(void)
{
	if(g_evteng_event_commenced && !g_evteng_sending_station_ID)
	{
		bool repeat = true;
		loadCurrentPatternMorse(&repeat, CALLER_AUTOMATED_EVENT);
	}
}

/**
 * Adapt completeTimeString() to a volatile time source by first taking a snapshot.
 *
 * @param partialString Partial time string supplied by the caller.
 * @param currentEpoch Volatile time source to snapshot.
 * @return Pointer returned by completeTimeString() for the snapped epoch value.
 */
static const char *completeTimeString_volatile(const char *partialString, volatile time_t *currentEpoch)
{
	time_t epoch = atomic_read_time(currentEpoch);
	return completeTimeString(partialString, &epoch);
}

/**
 * Parse a +HHH or +HHH:MM clock offset used by serial clock-setting commands.
 *
 * @param offsetString Offset string to parse.
 * @param hours Optional output pointer for the parsed hour component.
 * @param minutes Optional output pointer for the parsed minute component.
 * @param hasMinutes Optional output flag indicating whether a :MM suffix was supplied.
 * @return true on success, false if the string is not a valid offset.
 */
static bool parseClockHourMinuteOffset(const char *offsetString, uint16_t *hours, uint8_t *minutes, bool *hasMinutes)
{
	if(hours)
	{
		*hours = 0;
	}

	if(minutes)
	{
		*minutes = 0;
	}

	if(hasMinutes)
	{
		*hasMinutes = false;
	}

	if(!offsetString || (offsetString[0] != '+'))
	{
		return false;
	}

	const char *hours_str = offsetString + 1;
	if(!hours_str[0])
	{
		return false;
	}

	const char *colon = strchr(hours_str, ':');
	if(colon && strchr(colon + 1, ':'))
	{
		return false;
	}

	size_t hour_len = colon ? (size_t)(colon - hours_str) : strlen(hours_str);
	if(hour_len > 3)
	{
		return false;
	}

	uint16_t parsed_hours = 0;
	for(size_t i = 0; i < hour_len; i++)
	{
		if(!isdigit((unsigned char)hours_str[i]))
		{
			return false;
		}

		parsed_hours = (parsed_hours * 10) + (uint16_t)(hours_str[i] - '0');
	}

	if(parsed_hours > 480)
	{
		return false;
	}

	uint8_t parsed_minutes = 0;
	bool parsed_has_minutes = false;
	if(colon)
	{
		const char *minutes_str = colon + 1;
		size_t minute_len = strlen(minutes_str);
		if((minute_len == 0) || (minute_len > 2))
		{
			return false;
		}

		parsed_has_minutes = true;

		for(size_t i = 0; i < minute_len; i++)
		{
			if(!isdigit((unsigned char)minutes_str[i]))
			{
				return false;
			}

			parsed_minutes = (parsed_minutes * 10) + (uint8_t)(minutes_str[i] - '0');
		}

		if(parsed_minutes > 59)
		{
			return false;
		}
	}

	if(hours)
	{
		*hours = parsed_hours;
	}

	if(minutes)
	{
		*minutes = parsed_minutes;
	}

	if(hasMinutes)
	{
		*hasMinutes = parsed_has_minutes;
	}

	return true;
}

/**
 * Round an epoch to the nearest requested boundary without moving earlier than a minimum.
 *
 * @param epoch Epoch value to align.
 * @param boundary Boundary size in seconds.
 * @param minimumEpoch Minimum acceptable aligned value.
 * @return Aligned epoch value.
 */
static time_t alignEpochToNearestBoundary(time_t epoch, time_t boundary, time_t minimumEpoch)
{
	if(!boundary)
	{
		return epoch;
	}

	time_t aligned = ((epoch + (boundary / 2)) / boundary) * boundary;
	if(aligned < minimumEpoch)
	{
		aligned = ((minimumEpoch + boundary - 1) / boundary) * boundary;
	}

	return aligned;
}

/**
 * Resolve a user-supplied +hours or +hours:minutes offset into an absolute epoch.
 *
 * @param offsetString Offset string to resolve.
 * @param baseEpoch Base epoch from which the offset is applied.
 * @param baseEpochError Error text to use when the base epoch is invalid.
 * @param suppressBaseEpochError true to suppress the base-epoch error message.
 * @param hourBoundary Alignment boundary used for whole-hour offsets.
 * @param minuteBoundary Alignment boundary used for hour:minute offsets.
 * @param resolvedEpoch Optional output pointer for the resolved epoch.
 * @param errMsg Optional output buffer for a user-facing error string.
 * @return true on success, false on invalid input or invalid base time.
 */
static bool resolveClockOffsetToEpoch(const char *offsetString, time_t baseEpoch, const char *baseEpochError, bool suppressBaseEpochError, time_t hourBoundary, time_t minuteBoundary, time_t *resolvedEpoch, char *errMsg)
{
	if(resolvedEpoch)
	{
		*resolvedEpoch = 0;
	}

	if(baseEpoch < MINIMUM_VALID_EPOCH)
	{
		if(errMsg)
		{
			if(suppressBaseEpochError)
			{
				errMsg[0] = '\0';
			}
			else
			{
				strcpy(errMsg, baseEpochError ? baseEpochError : "* Err: Invalid offset!\n");
			}
		}

		return false;
	}

	uint16_t hours = 0;
	uint8_t minutes = 0;
	bool hasMinutes = false;
	if(!parseClockHourMinuteOffset(offsetString, &hours, &minutes, &hasMinutes))
	{
		if(errMsg)
		{
			strcpy(errMsg, "* Err: Invalid offset!\n");
		}

		return false;
	}

	time_t target = baseEpoch + ((time_t)hours * HOUR) + ((time_t)minutes * MINUTE);
	time_t boundary = hasMinutes ? minuteBoundary : hourBoundary;
	time_t alignedTarget = alignEpochToNearestBoundary(target, boundary, baseEpoch);

	if(resolvedEpoch)
	{
		*resolvedEpoch = alignedTarget;
	}

	if(errMsg)
	{
		if(alignedTarget != target)
		{
			strcpy(errMsg, TEXT_ALERT_TIME_ADJUSTED_TXT);
		}
		else
		{
			errMsg[0] = '\0';
		}
	}

	return true;
}

/**
 * Snap the saved Classic-event start time down to the previous 5-minute slot.
 *
 * @param notice Optional buffer that receives the user-facing adjustment notice.
 * @param noticeSize Size of the notice buffer.
 * @return true if the saved start time was changed, false otherwise.
 */
static bool alignSavedClassicStartTimeIfNeeded(char *notice, size_t noticeSize)
{
	time_t savedStartEpoch = atomic_read_time(&g_event_start_epoch);
	time_t remainder = savedStartEpoch % ((time_t)5 * MINUTE);

	if(notice && noticeSize)
	{
		notice[0] = '\0';
	}

	if((savedStartEpoch <= MINIMUM_VALID_EPOCH) || !remainder)
	{
		return false;
	}

	savedStartEpoch -= remainder;
	persistClockEpochValue(&g_evteng_loaded_start_epoch, &g_event_start_epoch, savedStartEpoch, Event_start_epoch, (void *)&g_event_start_epoch);

	if(notice && noticeSize)
	{
		strncpy(notice, TEXT_ERR_ALIGNED_TO_5MIN_TXT, noticeSize - 1);
		notice[noticeSize - 1] = '\0';
	}

	return true;
}

/**
 * Persist a clock value to both runtime state and EEPROM in one helper call.
 *
 * @param loadedEpoch Loaded-event epoch variable to update.
 * @param savedEpoch Saved epoch variable to update.
 * @param epoch New epoch value.
 * @param eeVar EEPROM field that should be updated.
 * @param eeValue Pointer to the value passed through to EEPROM storage.
 */
static void persistClockEpochValue(volatile time_t *loadedEpoch, volatile time_t *savedEpoch, time_t epoch, EE_var_t eeVar, void *eeValue)
{
	atomic_write_time_pair(loadedEpoch, savedEpoch, epoch, epoch);
	g_ee_mgr.updateEEPROMVar(eeVar, eeValue);
}

/**
 * Acknowledge a cloned clock update and fold it into the clone-session checksum.
 *
 * @param reply Reply string to send over the serial bus.
 * @param epoch Epoch value that should contribute to the checksum.
 */
static void acknowledgeClonedClockValue(const char *reply, time_t epoch)
{
	sb_send_string((char *)reply);
	atomic_write_u16(&g_programming_countdown, PROGRAMMING_MESSAGE_TIMEOUT_PERIOD);
	g_event_checksum += epoch;
}

/**
 * Clear clone/programming UI latches without rebooting or changing settings.
 */
static void clearCloneUiLatch(void)
{
	atomic_write_u16(&g_send_clone_success_countdown, 0);
	atomic_write_u16(&g_programming_countdown, 0);
	atomic_write_u16(&g_programming_msg_throttle, 0);
	g_cloningInProgress = false;
	g_defer_cloned_event_start = false;
}

/**
 * Report compact UI and clone state for automated tests.
 */
static void reportUiDiagnostics(void)
{
	sprintf(g_tempStr, "* UI cs=%u cl=%u df=%u pc=%u pt=%u\n",
	        atomic_read_u16(&g_send_clone_success_countdown),
	        g_cloningInProgress ? 1 : 0,
	        g_defer_cloned_event_start ? 1 : 0,
	        atomic_read_u16(&g_programming_countdown),
	        atomic_read_u16(&g_programming_msg_throttle));
	sb_send_master_string(g_tempStr);

	sprintf(g_tempStr, "* UI ms=%u mc=%u ee=%u ec=%u ru=%u fs=%u\n",
	        g_isMaster ? 1 : 0,
	        atomic_read_u16(&isMasterCountdownSeconds),
	        g_evteng_event_enabled ? 1 : 0,
	        g_evteng_event_commenced ? 1 : 0,
	        g_evteng_run_event_until_canceled ? 1 : 0,
	        g_foreground_start_event ? 1 : 0);
	sb_send_master_string(g_tempStr);
}

/**
 * Queue counted button presses for the normal foreground button dispatcher.
 */
static bool injectUiButtonPresses(const char *text)
{
	if(!text || !text[0])
	{
		return false;
	}

	char *end = NULL;
	long presses = strtol(text, &end, 10);
	if((end == text) || (end && *end) || (presses < 1) || (presses > 9))
	{
		return false;
	}

	atomic_write_u16(&g_foreground_handle_counted_presses, (uint16_t)presses);
	return true;
}

/**
 * Reset day tracking and restart event scheduling after a local clock update.
 */
static void finalizeLocalClockUpdate(void)
{
	cancelManualTransientState();
	g_days_to_run = 1;
	g_schedule_day_index = 0;
	startEventUsingRTC();
}
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
