OpenARDF/SignalSlinger/Software/AVR128DA28/SignalSlinger/src/morse.cpp

/*
 *  MIT License
 *
 *  Copyright (c) 2026 DigitalConfections
 *
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
 *  THE SOFTWARE IS PROVIDED "AS IS", WITHOUT WARRANTY OF ANY KIND, EXPRESS OR
 *  IMPLIED, INCLUDING BUT NOT LIMITED TO THE WARRANTIES OF MERCHANTABILITY,
 *  FITNESS FOR A PARTICULAR PURPOSE AND NONINFRINGEMENT. IN NO EVENT SHALL THE
 *  AUTHORS OR COPYRIGHT HOLDERS BE LIABLE FOR ANY CLAIM, DAMAGES OR OTHER
 *  LIABILITY, WHETHER IN AN ACTION OF CONTRACT, TORT OR OTHERWISE, ARISING FROM,
 *  OUT OF OR IN CONNECTION WITH THE SOFTWARE OR THE USE OR OTHER DEALINGS IN THE
 *  SOFTWARE.
 */

/*
 * Morse-code generation helpers shared across the firmware.
 *
 * This module contains support functions for:
 * - incremental Morse timing and carrier gating
 * - estimating message duration from code speed
 * - tracking which subsystem currently owns the Morse generator
 *
 * RF keying, throttling, and transmission scheduling belong elsewhere.
 */

#include "morse.h"
#include <stddef.h>

/**
 * Describe the encoded timing for a single Morse symbol sequence.
 *
 * `pattern` stores dits and dahs from least-significant bit upward, while the
 * length fields describe how many symbols are valid and how many Morse elements
 * the full character consumes.
 */
typedef struct
{
	uint8_t pattern;
	uint8_t lengthInSymbols;
	uint8_t lengthInElements;
} MorseCharacter;

/* Forward lookup for character-to-Morse metadata. */
MorseCharacter getMorseChar(char c);

static callerID_t g_lastCallerID = NO_CALLER;

/* Sentinel values used to distinguish spacing and forced-key cases from normal symbol patterns. */
#define SOLID_KEYDOWN 0xFF
#define INTER_CHAR_SPACE 0xFE
#define INTER_WORD_SPACE 0xFD

/**
 * Report which subsystem most recently claimed the Morse generator.
 *
 * @return The last caller identifier passed to `makeMorse()`.
 */
callerID_t lastMorseCaller(void)
{
	return g_lastCallerID;
}

/**
 * Load or advance the incremental Morse encoder.
 *
 * Pass a non-null string to start encoding a new message. Thereafter, call the
 * function once per Morse element interval with `s == NULL` to advance the
 * internal state machine; each call returns whether the CW carrier should be on
 * for that element.
 *
 * The encoder keeps its own static progress state so it can be ticked from a
 * timer-driven foreground loop without rebuilding the message state on each call.
 *
 * @param s Message to load, or NULL to advance the current transmission.
 * @param repeating Optional in/out flag controlling whether the message repeats.
 * @param finished Optional output flag set when the current message has finished.
 * @param caller Identifier for the subsystem using the Morse generator.
 * @return true when the carrier should be keyed during the current element.
 */
bool makeMorse(char *s, bool *repeating, bool *finished, callerID_t caller)
{
	static char *str = NULL;
	static char c = ' ';
	static bool repeat = true;
	static MorseCharacter morseInProgress;
	static uint8_t charIndex;    /* letters, numbers, punctuation */
	static uint8_t symbolIndex;  /* dits and dahs */
	static uint8_t elementIndex; /* units of time: dit = 1, dah = 3, intersymbol = 1, intercharacter = 3, etc. */
	static uint8_t addedSpace;   /* adds additional time to make an inter-character space */
	static bool completedString = true;
	static bool carrierOn = false;
	static bool holdKeyDown = false;

	/* Ignore ticks from a caller that does not own the current encoder state. */
	if(!s && (caller != g_lastCallerID))
	{
		return false;
	}

	if(s) /* load a new NULL-terminated string to send */
	{
		holdKeyDown = false;

		if(repeating)
		{
			repeat = *repeating;
		}

		if(caller != g_lastCallerID)
		{
			/* A new caller takes ownership and forces any previous transmission to stop. */
			g_lastCallerID = caller;
			str = NULL;
			completedString = true;
			if(finished)
			{
				*finished = true;
			}
		}

		if(*s)
		{
			/* Prime the state machine with the first character of the new message. */
			str = s;
			c = str[0];
			morseInProgress = getMorseChar(*str);
			charIndex = 0;
			symbolIndex = 0;
			elementIndex = 0;
			addedSpace = 0;
			completedString = false;
		}

		carrierOn = OFF;
		return (OFF);
	}
	else if(str)
	{
		if(repeating)
		{
			*repeating = repeat;
		}

		if(completedString)
		{
			if(finished)
			{
				*finished = true;
				holdKeyDown = false;
			}
			return (OFF);
		}

		if(elementIndex)
		{
			/* Stay in the current on/off phase until the element countdown expires. */
			elementIndex--;
		}
		else if(carrierOn && !holdKeyDown) /* carrier is on, so turn it off and wait appropriate amount of space */
		{
			carrierOn = false;
			/* wait one element = inter-symbol space */
			if(addedSpace)
			{
				elementIndex = addedSpace;
				addedSpace = 0;
			}
			/* wait inter-character space */
		}
		else /* carrier is off, so turn it on and get next symbol */
		{
			if(symbolIndex >= morseInProgress.lengthInSymbols)
			{
				/* The current character is complete; advance to the next one in the string. */
				c = (*(str + ++charIndex));

				if(!c) /* wrap to beginning of text */
				{
					if(repeat)
					{
						c = *str;
						charIndex = 0;
					}
					else
					{
						str = NULL;
						carrierOn = OFF;
						completedString = true;
						if(finished)
						{
							*finished = true;
						}
						holdKeyDown = false;
						return (OFF);
					}
				}

				morseInProgress = getMorseChar(c);
				symbolIndex = 0;
			}

			if(morseInProgress.pattern < INTER_WORD_SPACE)
			{
				/* Normal Morse symbols encode dits as 0 and dahs as 1 bits. */
				bool isDah = morseInProgress.pattern & (1 << symbolIndex++);

				if(isDah)
				{
					elementIndex = 2;
				}
				else
				{
					elementIndex = 0;
				}

				carrierOn = true;

				if(symbolIndex >= morseInProgress.lengthInSymbols)
				{
					addedSpace = 2;
				}
			}
			else
			{
				/* Spacing pseudo-characters consume time without keying the carrier. */
				uint8_t sym = morseInProgress.lengthInSymbols;
				symbolIndex = 255; /* ensure the next character gets read */
				carrierOn = false;
				if(sym >= 4)
				{
					elementIndex = morseInProgress.lengthInSymbols - 4;
				}
				else
				{
					elementIndex = 0;
				}
			}
		}

		/* '<' keeps the key held continuously instead of following symbol timing. */
		if(c == '<') /* constant tone */
		{
			holdKeyDown = true;
		}
		else
		{
			holdKeyDown = false;
		}
	}

	if(finished)
	{
		*finished = completedString;
	}

	if(holdKeyDown)
	{
		return (true);
	}
	else
	{
		return (carrierOn);
	}
}

/**
 * Estimate how long a message will take to send at a given code speed.
 *
 * The calculation uses the per-character element counts from `getMorseChar()`
 * and adds the standard inter-character spacing for keyed symbols.
 *
 * @param str Null-terminated text to evaluate.
 * @param spd Code speed in words per minute.
 * @return Estimated transmit time in milliseconds.
 */
uint16_t timeRequiredToSendStrAtWPM(char *str, uint16_t spd)
{
	uint8_t elements = 0;
	MorseCharacter m;
	char c;

	for(int i = 0; i < 20; i++)
	{
		c = str[i];
		if(!c)
		{
			break;
		}
		m = getMorseChar(c);
		if(m.pattern < INTER_WORD_SPACE)
		{
			/* Keyed characters need the trailing inter-character gap in addition to symbol timing. */
			elements += 3;
		}
		elements += m.lengthInElements;
	}

	return (elements * WPM_TO_MS_PER_DOT(spd));
}

/**
 * Look up the Morse timing metadata for a character.
 *
 * `pattern` stores symbols from least-significant bit to most-significant bit,
 * where 0 represents a dit and 1 represents a dah. `lengthInElements` includes
 * the symbol lengths and any intra-character spacing needed to send that entry.
 *
 * Special pseudo-characters such as space, `|`, and `<` are also recognized so
 * the state machine can model word gaps and a sustained key-down condition.
 *
 * @param c Character to translate.
 * @return Morse metadata for `c`, or an all-zero entry when unsupported.
 */
MorseCharacter getMorseChar(char c)
{
	MorseCharacter morse;

	switch(c)
	{
		case 'A':
		{
			morse.pattern = 0x02; /* 0000 0010; */
			morse.lengthInSymbols = 2;
			morse.lengthInElements = 5;
		}
		break;

		case 'B':
		{
			morse.pattern = 0x01; /* 0000 0001; */
			morse.lengthInSymbols = 4;
			morse.lengthInElements = 9;
		}
		break;

		case 'C':
		{
			morse.pattern = 0x05; /* 0000 0101; */
			morse.lengthInSymbols = 4;
			morse.lengthInElements = 11;
		}
		break;

		case 'D':
		{
			morse.pattern = 0x01; /* 0000 0001; */
			morse.lengthInSymbols = 3;
			morse.lengthInElements = 7;
		}
		break;

		case 'E':
		{
			morse.pattern = 0x00; /* 0000 0000; */
			morse.lengthInSymbols = 1;
			morse.lengthInElements = 1;
		}
		break;

		case 'F':
		{
			morse.pattern = 0x04; /* 0000 0100; */
			morse.lengthInSymbols = 4;
			morse.lengthInElements = 9;
		}
		break;

		case 'G':
		{
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
		{
			morse.pattern = 0x1f; /* 0001 1111; */
			morse.lengthInSymbols = 5;
			morse.lengthInElements = 19;
		}
		break;

		default:
		{
			morse.pattern = 0x0000; /* 0000 0000; */
			morse.lengthInSymbols = 0;
			morse.lengthInElements = 0;
		}
		break;
	}

	return (morse);
}
