OpenARDF/SignalSlinger/Software/AVR128DA28/SignalSlinger/src/transmitter.cpp

/*
 *  MIT License
 *
 *  Copyright (c) 2026 DigitalConfections
 *
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
 *  THE SOFTWARE IS PROVIDED "AS IS", WITHOUT WARRANTY OF ANY KIND, EXPRESS OR
 *  IMPLIED, INCLUDING BUT NOT LIMITED TO THE WARRANTIES OF MERCHANTABILITY,
 *  FITNESS FOR A PARTICULAR PURPOSE AND NONINFRINGEMENT. IN NO EVENT SHALL THE
 *  AUTHORS OR COPYRIGHT HOLDERS BE LIABLE FOR ANY CLAIM, DAMAGES OR OTHER
 *  LIABILITY, WHETHER IN AN ACTION OF CONTRACT, TORT OR OTHERWISE, ARISING FROM,
 *  OUT OF OR IN CONNECTION WITH THE SOFTWARE OR THE USE OR OTHER DEALINGS IN THE
 *  SOFTWARE.
 */

/*
 * RF transmitter control helpers.
 *
 * This module contains support functions for:
 * - initializing and restarting the Si5351-backed transmit clock path
 * - enabling or disabling RF-related power rails and support hardware
 * - keying, unkeying, and retuning the transmitter
 *
 * Event scheduling and higher-level transmit policy belong elsewhere.
 */

#include "serial_latency.h"
#include <string.h>
#include <stdlib.h>
#include <avr/eeprom.h>
#include "transmitter.h"
#include "port.h"
#include "binio.h"
#include "tcb.h"
#include "globals.h"

static const uint8_t TX_POWER_ON_INIT_RETRY_COUNT = 10;
static const uint8_t TX_CONTROL_RETRY_COUNT = 5;
static const uint16_t TX_POWER_SETTLE_DELAY_MS = 100;

static volatile bool g_tx_initialized = false;
volatile Frequency_Hz g_80m_frequency = EEPROM_FREQUENCY_DEFAULT;
volatile uint16_t g_80m_power_level_mW = EEPROM_TX_80M_POWER_MW_DEFAULT;
volatile Frequency_Hz g_rtty_offset = EEPROM_RTTY_OFFSET_FREQUENCY_DEFAULT;

static Frequency_Hz g_calibration_frequency_hz = RF_CALIBRATION_DEFAULT_FREQUENCY_HZ;
static Frequency_Hz g_active_calibration_frequency_hz = RF_CALIBRATION_DEFAULT_FREQUENCY_HZ;
static volatile bool g_calibration_carrier_active = false;
/* A calibration session may temporarily power and key an otherwise idle unit.
 * Retain the entry state so FRE C X can restore it exactly. */
static bool g_calibration_restore_initialized = false;
static bool g_calibration_restore_keyed = false;
static bool g_calibration_restore_valid = false;

static volatile bool g_drain_voltage_enabled = false;
static volatile bool g_transmitter_keyed = false;
static volatile bool g_disable_transmissions = false;

volatile bool g_enable_boost_regulator = false;

/*
 * Runtime role select for the shared auxiliary switch:
 * - HW_TARGET_3_5 defined: battery control and fan control are separate outputs,
 *   so this flag affects only the external-battery/charging path.
 * - HW_TARGET_3_5 not defined: the board has one shared auxiliary switched output;
 *   true routes that output to external-battery/charging support, false repurposes
 *   the same output for temperature-controlled fan drive.
 */
volatile bool g_enable_external_battery_control = true;

static_assert(RF_CALIBRATION_MIN_FREQUENCY_HZ == SI5351_CLKOUT_MIN_FREQ,
	          "RF calibration minimum must match the Si5351 library");
static_assert(RF_CALIBRATION_MAX_FREQUENCY_HZ == SI5351_CLKOUT_MAX_FREQ,
	          "RF calibration maximum must match the Si5351 library");

/**
 * Initialize the transmitter using the currently stored frequency.
 *
 * @param leave_clock_off true to leave the output clock disabled after setup.
 * @return true on success, false on failure.
 */
bool init_transmitter(bool leave_clock_off);

/**
 * Initialize the transmitter after first updating the stored working frequency.
 *
 * @param freq Frequency to remember and program.
 * @param leave_clock_off true to leave the output clock disabled after setup.
 * @return true on success, false on failure.
 */
bool init_transmitter(Frequency_Hz freq, bool leave_clock_off);

/**
 * Shut down the transmitter and its associated clock generator communications.
 */
void shutdown_transmitter(void);

/**
 * Power the transmitter back on and restart Si5351 communications.
 */
void restart_transmitter(void);

/*
 * This function sets the VFO frequency (CLK0 of the Si5351) based on the intended frequency passed in by the parameter (freq),
 * and the VFO configuration in effect. The VFO  frequency might be above or below the intended  frequency, depending on the VFO
 * configuration setting in effect for the radio band of the frequency.
 * Update the oscillator with a new transmit frequency.  The caller
 * may request that the clock remain disabled after programming.
 */
bool txSetFrequency(Frequency_Hz *freq, bool leaveClockOff)
{
	bool err = true;

	if(!freq)
		return (err);

	if(!g_tx_initialized)
	{
		g_80m_frequency = *freq;
		g_calibration_carrier_active = false;
		return false;
	}

	if((*freq < TX_MAXIMUM_FREQUENCY) && (*freq > TX_MINIMUM_FREQUENCY)) /* 80m */
	{
		if(!si5351_set_freq(*freq, TX_CLOCK_HF_0, leaveClockOff))
		{
			g_80m_frequency = *freq;
			g_calibration_carrier_active = false;
			err = false;
		}
	}

	return (err);
}

bool txSetCalibrationFrequency(Frequency_Hz frequency)
{
	if(!rfCalibrationFrequencyIsValid(frequency))
		return true;

	g_calibration_frequency_hz = rfCalibrationNormalizeFrequencyHz(frequency);
	return false;
}

Frequency_Hz txGetCalibrationFrequency(void)
{
	return g_calibration_frequency_hz;
}

Frequency_Hz txGetAppliedCalibrationFrequency(void)
{
	return g_calibration_carrier_active ? g_active_calibration_frequency_hz :
	                                      g_calibration_frequency_hz;
}

bool txRestoreCalibrationCorrectionPpb(int32_t correction_ppb)
{
	if(!rfCalibrationCorrectionIsValid(correction_ppb))
		return true;

	si5351_set_correction(correction_ppb);
	return false;
}

int32_t txGetCalibrationCorrectionPpb(void)
{
	return si5351_get_correction();
}

int32_t txGetCalibrationOffsetHz(void)
{
	return rfCalibrationOffsetHzForCorrection(txGetAppliedCalibrationFrequency(),
	                                         txGetCalibrationCorrectionPpb());
}

bool txCalibrationCarrierActive(void)
{
	return g_calibration_carrier_active;
}

/* Start or retune a keyed calibration carrier as one transaction. A session
 * entered from idle owns the temporary transmitter power and FRE C X returns
 * that hardware to idle; frequency and correction changes retain the original
 * entry state. */
static bool applyCalibrationCorrectionPpb(int32_t requested_correction_ppb)
{
	if(!rfCalibrationCorrectionIsValid(requested_correction_ppb))
		return true;

	const bool was_calibration_active = g_calibration_carrier_active;
	const bool entry_initialized = was_calibration_active ?
		g_calibration_restore_initialized : g_tx_initialized;
	const bool entry_keyed = was_calibration_active ?
		g_calibration_restore_keyed : g_transmitter_keyed;

	if(!g_tx_initialized)
	{
		if(!powerToTransmitter(true) || !g_tx_initialized)
		{
			powerToTransmitter(false);
			return true;
		}
	}

	const int32_t previous_correction_ppb = si5351_get_correction();
	const Frequency_Hz previous_frequency = was_calibration_active ?
		g_active_calibration_frequency_hz : g_80m_frequency;
	const bool was_keyed = g_transmitter_keyed;

	if(was_keyed)
	{
		keyTransmitter(false);
		if(g_transmitter_keyed)
			return true;
	}

	si5351_set_correction(requested_correction_ppb);
	bool failed = si5351_set_freq(g_calibration_frequency_hz, TX_CLOCK_HF_0, true);
	if(!failed)
		failed = !keyTransmitter(true);

	if(!failed)
	{
		if(!was_calibration_active)
		{
			g_calibration_restore_initialized = entry_initialized;
			g_calibration_restore_keyed = entry_keyed;
			g_calibration_restore_valid = true;
		}
		g_active_calibration_frequency_hz = g_calibration_frequency_hz;
		g_calibration_carrier_active = true;
		return false;
	}

	if(g_transmitter_keyed)
		keyTransmitter(false);
	si5351_set_correction(previous_correction_ppb);
	si5351_set_freq(previous_frequency, TX_CLOCK_HF_0, true);
	if(was_keyed)
		keyTransmitter(true);
	g_calibration_carrier_active = was_calibration_active;
	if(!was_calibration_active && !entry_initialized)
		powerToTransmitter(false);
	return true;
}

bool txStartCalibrationCarrier(void)
{
	return applyCalibrationCorrectionPpb(si5351_get_correction());
}

bool txApplyCalibrationOffsetHz(int32_t offset_hz)
{
	int32_t requested_correction_ppb;
	if(!rfCalibrationCorrectionForOffsetHz(g_calibration_frequency_hz,
	                                       offset_hz,
	                                       &requested_correction_ppb))
		return true;

	return applyCalibrationCorrectionPpb(requested_correction_ppb);
}

bool txExitCalibrationCarrier(void)
{
	if(!g_calibration_carrier_active)
		return false;
	if(!g_tx_initialized)
	{
		g_calibration_carrier_active = false;
		g_calibration_restore_valid = false;
		return false;
	}

	const bool restore_initialized = g_calibration_restore_valid ?
		g_calibration_restore_initialized : true;
	const bool restore_keyed = g_calibration_restore_valid ?
		g_calibration_restore_keyed : false;
	if(g_transmitter_keyed)
	{
		keyTransmitter(false);
		if(g_transmitter_keyed)
			return true;
	}

	if(si5351_set_freq(g_80m_frequency, TX_CLOCK_HF_0, true))
	{
		si5351_set_freq(g_active_calibration_frequency_hz, TX_CLOCK_HF_0, true);
		keyTransmitter(true);
		return true;
	}

	if(restore_keyed && !keyTransmitter(true))
	{
		si5351_set_freq(g_active_calibration_frequency_hz, TX_CLOCK_HF_0, true);
		keyTransmitter(true);
		return true;
	}

	g_calibration_carrier_active = false;
	g_calibration_restore_valid = false;
	if(!restore_initialized)
		powerToTransmitter(false);
	return false;
}

/**
 * Globally enable or disable all RF transmissions.
 *
 * When disabled, the RF path is powered down so callers cannot accidentally
 * emit RF even if they later request keying or power.
 *
 * @param disabled true to block transmissions and power down the RF path.
 */
void setDisableTransmissions(bool disabled)
{
	if(disabled)
	{
		g_disable_transmissions = true;
		powerToTransmitter(OFF);
	}
	else
	{
		g_disable_transmissions = false;
	}
}

bool getDisableTransmissions(void)
{
	return (g_disable_transmissions);
}

/**
 * Apply or remove power from the RF chain and related control lines.
 *
 * When enabling, the shared support rails are brought up, the Si5351 path is
 * reinitialized, and the working frequency is restored. When disabling, the
 * clock generator and keyed-output state are torn down.
 *
 * @param state true to power the transmitter path, false to shut it down.
 * @return true when the requested state is reached successfully.
 */
bool powerToTransmitter(bool state)
{
	if(state && transmitterThermallyBlocked()) state = false;
	bool success = true;

	/* BAT X 2 disables the internal RF chain but still uses the external-control
	 * switch to power any attached external device with the same event timing. */
	if(g_enable_external_battery_control)
		setExtBatLoadSwitch(state, TRANSMITTER);

	if(g_disable_transmissions)
	{
		si5351_shutdown_comms();
#ifdef HW_TARGET_3_5
#else
		setBoostEnable(OFF);
#endif
		setFETDriverLoadSwitch(OFF, TRANSMITTER);
		setSignalGeneratorEnable(OFF, TRANSMITTER);
		g_tx_initialized = false;
		g_transmitter_keyed = false;
		g_calibration_carrier_active = false;
		g_calibration_restore_valid = false;
	}
	else
	{
		if(!state)
		{
			si5351_shutdown_comms();
		}

		setSignalGeneratorEnable(state, TRANSMITTER);

#ifdef HW_TARGET_3_5
#else
		if(g_enable_boost_regulator)
			setBoostEnable(state);
#endif
		setFETDriverLoadSwitch(state, TRANSMITTER);

		if(state)
		{
			int tries = TX_POWER_ON_INIT_RETRY_COUNT;

			util_delay_ms(0);
			while(util_delay_ms(TX_POWER_SETTLE_DELAY_MS))
				;
			while(tries && !init_transmitter(g_80m_frequency, true))
			{
				--tries;
			}

			if(!tries)
			{
				success = false;
			}

			si5351_start_comms();
		}
		else
		{
			g_tx_initialized = false;
			g_transmitter_keyed = false;
			g_calibration_carrier_active = false;
			g_calibration_restore_valid = false;
		}
	}

	return (success);
}

/**
 * Key or unkey the transmitter output stage.
 *
 * The function retries clock-enable operations and will restart the transmitter
 * path if the Si5351 command does not succeed on the first attempt.
 *
 * @param on true to key the transmitter, false to unkey it.
 * @return true when the transmitter ends in the keyed state.
 */
bool keyTransmitter(bool on)
{
	SERIAL_LATENCY_SCOPE(LAT_KEY);
	if(on && transmitterThermallyBlocked()) on = false;
	if(g_tx_initialized)
	{
		int tries = TX_CONTROL_RETRY_COUNT;

		if(on)
		{
			if(!g_transmitter_keyed)
			{
				fet_driver(ON);
				while(--tries && !si5351_clock_enable(TX_CLOCK_HF_0, SI5351_CLK_ENABLED))
				{
					shutdown_transmitter();
					restart_transmitter();
				}

				if(tries)
				{
					g_transmitter_keyed = true;
				}
			}
		}
		else
		{
			if(g_transmitter_keyed)
			{
				while(--tries && !si5351_clock_enable(TX_CLOCK_HF_0, SI5351_CLK_DISABLED))
				{
					shutdown_transmitter();
					restart_transmitter();
				}

				if(tries)
				{
					g_transmitter_keyed = false;
				}
			}
		}
	}
	else
	{
		g_transmitter_keyed = false;
	}

	return (g_transmitter_keyed);
}

bool txIsKeyed(void)
{
	return g_transmitter_keyed;
}

bool txIsInitialized(void)
{
	return g_tx_initialized;
}

/**
 * Shut down the transmitter and its associated clock generator communications.
 */
void shutdown_transmitter(void)
{
	si5351_shutdown_comms();
	powerToTransmitter(OFF);
}

/**
 * Power the transmitter back on and restart Si5351 communications.
 */
void restart_transmitter(void)
{
	powerToTransmitter(ON);
	si5351_start_comms();
}

/**
 * Initialize the transmitter after first updating the stored working frequency.
 *
 * @param freq Frequency to remember and program.
 * @param leave_clock_off true to leave the output clock disabled after setup.
 * @return true on success, false on failure.
 */
bool init_transmitter(Frequency_Hz freq, bool leave_clock_off)
{
	g_80m_frequency = freq;
	return init_transmitter(leave_clock_off);
}

/**
 * Initialize the transmitter using the currently stored frequency.
 *
 * This programs the Si5351, configures its drive strength, and ensures the
 * selected transmit frequency is pushed into the active output path.
 *
 * @param leave_clock_off true to leave the output clock disabled after setup.
 * @return true on success, false on failure.
 */
bool init_transmitter(bool leave_clock_off)
{
	int tries = TX_CONTROL_RETRY_COUNT;

	while(--tries && si5351_init(SI5351_CRYSTAL_LOAD_6PF, 0))
		; /* Initialize SI5351 */

	if(!tries) // SI5351 initialization failed
	{
		return false;
	}

	tries = TX_CONTROL_RETRY_COUNT;

	while(--tries && !si5351_drive_strength(TX_CLOCK_HF_0, SI5351_DRIVE_2MA))
		; /* Initialize SI5351 */

	if(!tries) // SI5351 drive strength failed
	{
		return false;
	}

	tries = TX_CONTROL_RETRY_COUNT;

	while(--tries && !si5351_clock_enable(TX_CLOCK_HF_0, SI5351_CLK_DISABLED))
		; /* Initialize SI5351 */

	if(!tries) // SI5351 drive strength failed
	{
		return false;
	}
	else
	{
		g_tx_initialized = true;
	}

	tries = TX_CONTROL_RETRY_COUNT;

	while(--tries && (txSetFrequency((Frequency_Hz *)&g_80m_frequency, leave_clock_off)))
		; /* Initialize SI5351 */

	if(!tries) // SI5351 drive strength failed
	{
		return false;
	}

	return true;
}
