OpenARDF/SignalSlinger/Software/AVR128DA28/SignalSlinger/src/i2c.cpp

/*
 *  MIT License
 *
 *  Copyright (c) 2026 DigitalConfections
 *
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
 *  THE SOFTWARE IS PROVIDED "AS IS", WITHOUT WARRANTY OF ANY KIND, EXPRESS OR
 *  IMPLIED, INCLUDING BUT NOT LIMITED TO THE WARRANTIES OF MERCHANTABILITY,
 *  FITNESS FOR A PARTICULAR PURPOSE AND NONINFRINGEMENT. IN NO EVENT SHALL THE
 *  AUTHORS OR COPYRIGHT HOLDERS BE LIABLE FOR ANY CLAIM, DAMAGES OR OTHER
 *  LIABILITY, WHETHER IN AN ACTION OF CONTRACT, TORT OR OTHERWISE, ARISING FROM,
 *  OUT OF OR IN CONNECTION WITH THE SOFTWARE OR THE USE OR OTHER DEALINGS IN THE
 *  SOFTWARE.
 */

/*
 * Low-level I2C/TWI host helpers.
 *
 * This module contains support functions for:
 * - initializing the primary TWI host peripheral
 * - sending register-addressed writes and reads
 * - ending or shutting down an I2C session cleanly
 *
 * Device-specific register maps and higher-level retry policy belong elsewhere.
 */

#include "serial_latency.h"
#include "defs.h"
#include <util/twi.h>
#include <avr/power.h>
#include <avr/io.h>
#include <avr/sfr_defs.h>
#include <util/atomic.h>

#include "si5351.h"
#include "i2c.h"
#include "port.h"
#include "shared_state.h"

#ifdef TWI_BAUD
#undef TWI_BAUD
#endif

// #define TWI_BAUD(F_SCL, T_RISE)        (uint8_t)((((((float)F_CPU / (float)(F_SCL)) - 10 - (((float)(F_CPU) * (T_RISE))/1000000.0))) / 2))
// #define I2C_SCL_FREQ                    100000  /* Frequency [Hz] */

#define CLK_PER                                         24000000     // 24MHz default clock
#define TWI0_BAUD(F_SCL, T_RISE)                 ((((((float)CLK_PER / (float)F_SCL)) - 10 - ((float)CLK_PER * T_RISE))) / 2)
#define TWI1_BAUD(F_SCL, T_RISE)                 ((((((float)CLK_PER / (float)F_SCL)) - 10 - ((float)CLK_PER * T_RISE))) / 2)

#define I2C_SCL_FREQ                                    100000


enum {
	I2C_INIT = 0,
	I2C_ACKED,
	I2C_NACKED,
	I2C_READY,
	I2C_ERROR
};

volatile uint16_t g_i2c0_timeout_ticks = 200; 
volatile uint16_t g_i2c_failure_count = 0; /* Legacy */

/************************************************************************/
/* I2C_0                                                               */
/************************************************************************/

/**
 * Disable the primary I2C/TWI host interface.
 */
void I2C_0_Shutdown(void)
{
	/* Set bus state idle */
	TWI0.MSTATUS = TWI_BUSSTATE_IDLE_gc;
	TWI0.MCTRLA = 0;
}

/**
 * Initialize the primary I2C/TWI host interface.
 */
void I2C_0_Init(void)
{
	/* Select I2C pins PC2/PC3 */
	PORTMUX.TWIROUTEA &= 0x0A;
	PORTMUX.TWIROUTEA |= 0x02;
	
	/* Host Baud Rate Control */
//	TWI0.MBAUD = TWI0_BAUD((I2C_SCL_FREQ), 0.3);
	TWI0.MBAUD = (uint8_t)TWI0_BAUD(I2C_SCL_FREQ, 0);
	
	/* Enable TWI */
	TWI0.MCTRLA = TWI_ENABLE_bm;
	
	/* Initialize the address register */
	TWI0.MADDR = 0x00;
	
	/* Initialize the data register */
	TWI0.MDATA = 0x00;
	
	/* Set bus state idle */
	TWI0.MSTATUS = TWI_BUSSTATE_IDLE_gc;
	/* Select I2C pins PC2/PC3 */
	
	PORTC_set_pin_pull_mode(2, PORT_PULL_UP);
	PORTC_set_pin_pull_mode(3, PORT_PULL_UP);
}

/**
 * Wait for a write-phase I2C state transition.
 *
 * @return I2C state code describing ACK, NACK, ready, or error.
 */
static uint8_t i2c_0_WaitW(void)
{
	uint8_t state = I2C_INIT;
	uint32_t spin_guard = 60000UL;
	
	/* The timeout counter is serviced elsewhere by a periodic timer tick. */
	atomic_write_u16(&g_i2c0_timeout_ticks, 50);
	
	do
	{
		if(TWI0.MSTATUS & (TWI_WIF_bm | TWI_RIF_bm))
		{
			if(!(TWI0.MSTATUS & TWI_RXACK_bm))
			{
				/* client responded with ack - TWI goes to M1 state */
				state = I2C_ACKED;
			}
			else
			{
				/* address sent but no ack received - TWI goes to M3 state */
				state = I2C_NACKED;
			}
		}
		else if(TWI0.MSTATUS & (TWI_BUSERR_bm | TWI_ARBLOST_bm))
		{
			/* get here only in case of bus error or arbitration lost - M4 state */
			state = I2C_ERROR;
		}
	} while(!state && atomic_read_u16(&g_i2c0_timeout_ticks) && spin_guard--);
	
	if(!state)
	{
		state = I2C_ERROR;
		if(g_i2c_failure_count < UINT16_MAX) g_i2c_failure_count++;
	}
	
	return state;
}

/**
 * Wait for a read-phase I2C state transition.
 *
 * @return I2C state code describing ready or error.
 */
static uint8_t i2c_0_WaitR(void)
{
	uint8_t state = I2C_INIT;
	uint32_t spin_guard = 60000UL;
	
	atomic_write_u16(&g_i2c0_timeout_ticks, 50);
	
	do
	{
		if(TWI0.MSTATUS & (TWI_WIF_bm | TWI_RIF_bm))
		{
			state = I2C_READY;
		}
		else if(TWI0.MSTATUS & (TWI_BUSERR_bm | TWI_ARBLOST_bm))
		{
			/* get here only in case of bus error or arbitration lost - M4 state */
			state = I2C_ERROR;
		}
	} while(!state && atomic_read_u16(&g_i2c0_timeout_ticks) && spin_guard--);
	
	if(!state)
	{
		state = I2C_ERROR;
		if(g_i2c_failure_count < UINT16_MAX) g_i2c_failure_count++;
	}
	
	return state;
}

/**
 * Write one or more bytes to a register-addressed I2C peripheral.
 *
 * @param slaveAddr 7-bit slave address in write form.
 * @param regAddr Register address to send before the payload.
 * @param pData Pointer to the bytes to send.
 * @param len Number of payload bytes to send.
 * @return Number of payload bytes acknowledged, or `0xFF` if the slave address is NACKed.
 */
uint8_t I2C_0_SendData(uint8_t slaveAddr, uint8_t regAddr, uint8_t *pData, uint8_t len)
{
	SERIAL_LATENCY_SCOPE(LAT_I2C_WRITE);
	uint8_t retVal = (uint8_t) - 1;
	
	/* Send slave address */
	TWI0.MADDR = slaveAddr;
	if(i2c_0_WaitW() != I2C_ACKED)
	{
		I2C_0_EndSession();
		return retVal;
	}
	
	/* Send the register address */
	TWI0.MDATA = regAddr;
	if(i2c_0_WaitW() != I2C_ACKED)
	{
		I2C_0_EndSession();
		return retVal;
	}

	retVal = 0;
	if((len != 0) && (pData != null))
	{
		while(len--)
		{
			TWI0.MDATA = *pData;
			if(i2c_0_WaitW() == I2C_ACKED)
			{
				retVal++;
				pData++;
				if(!len) I2C_0_EndSession();
				continue;
			}
				else // did not get ACK after client address
				{
					I2C_0_EndSession();
					break;
				}
		}
	}
	
	return retVal;
}

/**
 * Read one or more bytes from a register-addressed I2C peripheral.
 *
 * @param slaveAddr 7-bit slave address in write form.
 * @param regAddr Register address to read from.
 * @param pData Destination buffer for received bytes.
 * @param len Number of bytes to receive.
 * @return Number of bytes received, or `0xFF` if the slave address is NACKed.
 */
uint8_t I2C_0_GetData(uint8_t slaveAddr, uint8_t regAddr, uint8_t *pData, uint8_t len)
{
	SERIAL_LATENCY_SCOPE(LAT_I2C_READ);
	uint8_t retVal = (uint8_t) -1;
	
	/* Send the client address for write */
	TWI0.MADDR = slaveAddr;
	if(i2c_0_WaitW() != I2C_ACKED)
	{
		I2C_0_EndSession();
		return retVal;
	}
	
	/* Send the register address */
	TWI0.MDATA = regAddr;
	if(i2c_0_WaitW() != I2C_ACKED)
	{
		I2C_0_EndSession();
		return retVal;
	}
	
	/* Send the client address for read */
	TWI0.MADDR = slaveAddr | 0x01;
	if(i2c_0_WaitW() != I2C_ACKED)
	{
		I2C_0_EndSession();
		return retVal;
	}
	
	retVal = 0;
	if((len != 0) && (pData !=null ))
	{
		while(len--)
		{
			if(i2c_0_WaitR() == I2C_READY)
			{
				*pData = TWI0.MDATA;
				TWI0.MCTRLB = (len == 0)? TWI_ACKACT_bm | TWI_MCMD_STOP_gc : TWI_MCMD_RECVTRANS_gc;
				retVal++;
				pData++;
				continue;
			}
				else
				{
					I2C_0_EndSession();
					break;
				}
			}
		}
	
	return retVal;
}

/**
 * Send a STOP condition to end the current I2C transaction.
 */
void I2C_0_EndSession(void)
{
	TWI0.MCTRLB = TWI_MCMD_STOP_gc;
}

/************************************************************************/
/* I2C_1                                                               */
/************************************************************************/

// void I2C_1_Shutdown(void)
// {
// 	/* Set bus state idle */
// 	TWI1.MSTATUS = TWI_BUSSTATE_IDLE_gc;
// 	TWI1.MCTRLA = 0;
// }
// 
// void I2C_1_Init(void)
// {
// 	/* Select I2C pins PB2/PB3 */
// 	PORTMUX.TWIROUTEA &= 0x03;
// 	PORTMUX.TWIROUTEA |= 0x08;
// 	
// 	/* Host Baud Rate Control */
// //	TWI1.MBAUD = TWI1_BAUD((I2C_SCL_FREQ), 0.3);
// 	TWI1.MBAUD = (uint8_t)TWI0_BAUD(I2C_SCL_FREQ, 0);
// 		
// 	/* Enable TWI */
// 	TWI1.MCTRLA = TWI_ENABLE_bm;
// 	
// 	/* Initialize the address register */
// 	TWI1.MADDR = 0x00;
// 	
// 	/* Initialize the data register */
// 	TWI1.MDATA = 0x00;
// 	
// 	/* Set bus state idle */
// 	TWI1.MSTATUS = TWI_BUSSTATE_IDLE_gc;
// 	
// 	PORTB_set_pin_pull_mode(2, PORT_PULL_UP);
// 	PORTB_set_pin_pull_mode(3, PORT_PULL_UP);
// }
// 
// static uint8_t i2c_1_WaitW(void)
// {
// 	uint8_t state = I2C_INIT;
// 	
// 	g_i2c1_timeout_ticks = 50;
// 	
// 	do
// 	{
// 		uint8_t stat = TWI1.MSTATUS;
// 		if(stat & (TWI_WIF_bm | TWI_RIF_bm))
// 		{
// 			if(!(stat & TWI_RXACK_bm))
// 			{
// 				/* client responded with ack - TWI goes to M1 state */
// 				state = I2C_ACKED;
// 			}
// 			else
// 			{
// 				/* address sent but no ack received - TWI goes to M3 state */
// 				state = I2C_NACKED;
// 			}
// 		}
// 		else if(stat & (TWI_BUSERR_bm | TWI_ARBLOST_bm))
// 		{
// 			/* get here only in case of bus error or arbitration lost - M4 state */
// 			state = I2C_ERROR;
// 		}
// 	} while(!state && g_i2c1_timeout_ticks);
// 	
// 	return state;
// }
// 
// static uint8_t I2C_1_WaitR(void)
// {
// 	uint8_t state = I2C_INIT;
// 	
// 	g_i2c0_timeout_ticks = 50;
// 	
// 	do
// 	{
// 		if(TWI1.MSTATUS & (TWI_WIF_bm | TWI_RIF_bm))
// 		{
// 			state = I2C_READY;
// 		}
// 		else if(TWI1.MSTATUS & (TWI_BUSERR_bm | TWI_ARBLOST_bm))
// 		{
// 			/* get here only in case of bus error or arbitration lost - M4 state */
// 			state = I2C_ERROR;
// 		}
// 	} while(!state && g_i2c0_timeout_ticks);
// 	
// 	return state;
// }
// 
// /* Returns how many bytes have been sent, -1 means NACK at address, 0 means client ACKed to client address */
// uint8_t I2C_1_SendData(uint8_t slaveAddr, uint8_t regAddr, uint8_t *pData, uint8_t len)
// {
// 	uint8_t retVal = (uint8_t) - 1;
// 	
// 	/* Send the slave address */
// 	TWI1.MADDR = slaveAddr & ~0x01;
// 	if(i2c_1_WaitW() != I2C_ACKED)
// 	{
// 		return retVal;
// 	}
// 	
// 	/* Send the register address */
// 	TWI1.MDATA = regAddr;	
// 	if(i2c_1_WaitW() != I2C_ACKED)
// 	{
// 		return retVal;
// 	}	
// 
// 	retVal = 0;
// 	if((len != 0) && (pData != null))
// 	{
// 		while(len--)
// 		{
// 			TWI1.MDATA = *pData;
// 			if(i2c_1_WaitW() == I2C_ACKED)
// 			{
// 				retVal++;
// 				pData++;
// 				if(!len) I2C_1_EndSession();
// 				continue;
// 			}
// 			else // did not get ACK after client address
// 			{
// 				break;
// 			}
// 		}
// 	}
// 	
// 	return retVal;
// }
// 
// 
// /* Returns how many bytes have been received, -1 means NACK at address */
// uint8_t I2C_1_GetData(uint8_t slaveAddr, uint8_t regAddr, uint8_t *pData, uint8_t len)
// {
// 	uint8_t retVal = (uint8_t) -1;
// 	
// 	/* Send the client address for write */
// 	TWI1.MADDR = slaveAddr;
// 	if(i2c_1_WaitW() != I2C_ACKED)
// 	{
// 		return retVal;
// 	}
// 	
// 	/* Send the register address */
// 	TWI1.MDATA = regAddr;	
// 	if(i2c_1_WaitW() != I2C_ACKED)
// 	{
// 		return retVal;
// 	}
// 	
// 	/* Send the client address for read */
// 	TWI1.MADDR = slaveAddr | 0x01;
// 	if(i2c_1_WaitW() != I2C_ACKED)
// 	{
// 		return retVal;	
// 	}
// 	
// 	retVal = 0;
// 	if((len != 0) && (pData !=null ))
// 	{
// 		while(len--)
// 		{
// 			if(I2C_1_WaitR() == I2C_READY)
// 			{
// 				*pData = TWI1.MDATA;
// 				TWI1.MCTRLB = (len == 0)? TWI_ACKACT_bm | TWI_MCMD_STOP_gc : TWI_MCMD_RECVTRANS_gc;
// 				retVal++;
// 				pData++;
// 				continue;
// 			}
// 			else
// 			break;
// 		}
// 	}
// 	
// 	return retVal;
// }
// 
// void I2C_1_EndSession(void)
// {
// 	TWI1.MCTRLB = TWI_MCMD_STOP_gc;
// }
