OpenARDF/SignalSlinger/Software/AVR128DA28/SignalSlinger/include/serialbus.h

/*
 *  MIT License
 *
 *  Copyright (c) 2026 DigitalConfections
 *
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
 *  THE SOFTWARE IS PROVIDED "AS IS", WITHOUT WARRANTY OF ANY KIND, EXPRESS OR
 *  IMPLIED, INCLUDING BUT NOT LIMITED TO THE WARRANTIES OF MERCHANTABILITY,
 *  FITNESS FOR A PARTICULAR PURPOSE AND NONINFRINGEMENT. IN NO EVENT SHALL THE
 *  AUTHORS OR COPYRIGHT HOLDERS BE LIABLE FOR ANY CLAIM, DAMAGES OR OTHER
 *  LIABILITY, WHETHER IN AN ACTION OF CONTRACT, TORT OR OTHERWISE, ARISING FROM,
 *  OUT OF OR IN CONNECTION WITH THE SOFTWARE OR THE USE OR OTHER DEALINGS IN THE
 *  SOFTWARE.
 */
/*
 * Simple serial inter-processor messaging helpers.
 *
 * This module contains support functions for:
 * - managing UART-backed transmit and receive buffers for serial commands
 * - queueing prompt, reply, and echo traffic
 * - exposing parsed receive buffers to foreground code
 *
 * Command semantics and application-level message handling belong elsewhere.
 */

#ifndef SERIALBUS_H_
#define SERIALBUS_H_

#include "defs.h"
#include "usart_basic.h"

#ifdef __cplusplus
extern "C"
{
#endif

#define SERIALBUS_USART USART_1

#define SERIALBUS_MAX_MSG_LENGTH 50
#define SERIALBUS_MIN_MSG_LENGTH 2 /* shortest message: GO */
#define SERIALBUS_MAX_MSG_FIELD_LENGTH 20
#define SERIALBUS_MAX_MSG_NUMBER_OF_FIELDS 3
#define SERIALBUS_NUMBER_OF_RX_MSG_BUFFERS 4
#define SERIALBUS_MAX_TX_MSG_LENGTH 41
#define SERIALBUS_NUMBER_OF_TX_MSG_BUFFERS 3
#define SERIALBUS_MAX_MSG_ID_LENGTH 3
#define SERIALBUS_MAX_MESHTASTIC_PREFIX_LENGTH 16

#define SERIALBUS_MAX_COMMANDLINE_LENGTH ((1 + SERIALBUS_MAX_MSG_FIELD_LENGTH) * SERIALBUS_MAX_MSG_NUMBER_OF_FIELDS)

#define SERIALBUS_POWERUP_DELAY_SECONDS 6

#define SERIALBUS_MIN_TX_INTERVAL_MS 100

#define SB_BAUD 9600

	// #define MYUBRR(b) ((F_CPU + b * 8L) / (b * 16L) - 1)

	// typedef enum
	// {
	// 	SB_EMPTY_BUFF,
	// 	SB_FULL_BUFF
	// } BufferState;

	/*  Serialbus Messages
	 *       Message formats:
	 *               CMD [a1 [a2]]
	 *
	 *               where
	 *                       CMD = command
	 *                       a1, a2 = optional arguments or data fields
	 *
	 */

	typedef enum
	{
		SB_MESSAGE_EMPTY = 0,

		/*	ARDUCON MESSAGE FAMILY (SERIAL MESSAGING) */
		SB_MESSAGE_SET_FOX = 'F' * 100 + 'O' * 10 + 'X',       /* Set the fox role to be used to define timing and signals */
		SB_MESSAGE_BATTERY = 'B' * 100 + 'A' * 10 + 'T',       /* Battery voltage and threshold setting */
		SB_MESSAGE_SET_STATION_ID = 'I' * 10 + 'D',            /* Sets amateur radio callsign text */
		SB_MESSAGE_GO = 'G' * 10 + 'O',                        /* Start/stop transmissions */
		SB_MESSAGE_CODE_SETTINGS = 'S' * 100 + 'P' * 10 + 'D', /* Set Morse code speeds */
		SB_MESSAGE_CLOCK = 'C' * 100 + 'L' * 10 + 'K',         /* Set or read the RTC */
		SB_MESSAGE_MASTER = 'M' * 100 + 'A' * 10 + 'S',        /* Set master role command */
		SB_MESSAGE_EVENT = 'E' * 100 + 'V' * 10 + 'T',         /* Set event */
		SB_MESSAGE_TX_FREQ = 'F' * 100 + 'R' * 10 + 'E',       /* Transmit frequency */
		SB_MESSAGE_PATTERN = 'P' * 100 + 'A' * 10 + 'T',       /* Set the transmit pattern */
		SB_MESSAGE_KEY = 'K' * 100 + 'E' * 10 + 'Y',           /* Key on/off */
		SB_MESSAGE_SLP = 'S' * 100 + 'L' * 10 + 'P',           /* Sleep */
		SB_MESSAGE_VER = 'V' * 100 + 'E' * 10 + 'R',           /* Version */
		SB_MESSAGE_INFO = 'I' * 100 + 'N' * 10 + 'F',          /* Machine-readable firmware information */
		SB_MESSAGE_RESET = 'R' * 100 + 'S' * 10 + 'T',         /* Software Reset */
		SB_MESSAGE_UPDATE = 'U' * 100 + 'P' * 10 + 'D',        /* Enter bootloader update mode */
		SB_MESSAGE_HELP = '?',                                 /* Help */
		SB_MESSAGE_TEMPERATURE = 'T' * 100 + 'M' * 10 + 'P',   /* Temperature information */
		SB_MESSAGE_FUNCTION = 'F' * 100 + 'U' * 10 + 'N',      /* Functionality setting */
		SB_MESSAGE_UI_DIAGNOSTICS = 'U' * 10 + 'I',            /* UI diagnostics and button injection */
		SB_MODE_MESH = 'M' * 100 + 'S' * 10 + 'H',             /* Meshtastic mode setting */
		SB_RX_CORRUPT = MAX_UINT16 - 3,                        /* UART reported damaged or lost input */
		SB_RX_IDLE_TIMEOUT = MAX_UINT16 - 2,                   /* Parser dropped a stale partial RX line */
		SB_INVALID_MESSAGE = MAX_UINT16,                       /* This value must never overlap a valid message ID */
		SB_CR_NO_DATA = MAX_UINT16 - 1                         /* This value must never overlap a valid message ID */
	} SBMessageID;

	typedef enum
	{
		SERIALBUS_MSG_UNKNOWN = 0,
		SERIALBUS_MSG_COMMAND,
		SERIALBUS_MSG_QUERY,
		SERIALBUS_MSG_REPLY,
		SERIALBUS_MSG_INVALID
	} SBMessageType;

	typedef enum
	{
		SB_FIELD1 = 0,
		SB_FIELD2 = 1
	} SBMessageField;

	typedef char SerialbusTxBuffer[SERIALBUS_MAX_TX_MSG_LENGTH];

	typedef struct
	{
		SBMessageType type;
		SBMessageID id;
		char fields[SERIALBUS_MAX_MSG_NUMBER_OF_FIELDS][SERIALBUS_MAX_MSG_FIELD_LENGTH];
	} SerialbusRxBuffer;

#define WAITING_FOR_UPDATE -1
/* Saturating receive error counters since reset, shared by the active UART. */
void serialbusRxErrors(uint16_t *overrun, uint16_t *framing, uint16_t *parity);

#define HELP_TEXT_TXT (char *)"\n* Commands:\n* > ? - List valid commands\n* > CLK [T|S|F|D [\"YYMMDDhhmmss\"]] - Read/set time/start/finish/days\n* > EVT [C|F|S] - Set event\n* > FOX [fox]- Set fox role\n* > FRE [frequency] - Set tx frequency\n* > FRE CF [kHz|MHz] - Read/set and key volatile calibration carrier\n* > FRE C [offset|X] - Calibrate/exit RF carrier\n* > ID [callsign] -  Set callsign\n* > KEY [1|0] - key down/up\n* > MAS [0|1] - Set Source or Target\n* > PAT [text] - Set xmit pattern\n* > SPD I|F|P [wpm] - Set ID code speed\n* > GO 0-3 - Start event\n* > BAT [T|X] [0-2] - Battery\n* > TMP [H [ON|OFF|n]|R [X|E]] - Temperature\n* > INF - Firmware information\n* > UI [S|C|P n|D|B samples|T [seconds]] - UI diagnostics\n* > UPD - Enter bootloader update mode\n\0"

	/**
	 * Configure the serial bus with a baud rate and USART instance.
	 */
	void serialbus_init(uint32_t baud, USART_Number_t usart);

	/**
	 * Discard any unread bytes currently waiting in the active USART RX register path.
	 */
	void serialbus_flush_rx(void);

	/**
	 * Immediately turns off receiver and flushes receive buffer
	 */
	void serialbus_disable(void);

	/**
	 * Reset any partially-parsed ISR RX state while preserving mesh-mode selection.
	 */
	void serialbus_reset_rx_parser(void);

	/**
	 * Synchronize the ISR-side RX echo/parser mesh-mode flag with foreground state.
	 */
	void serialbus_set_rx_mesh_mode(bool enabled);

	/**
	 * Allow or suppress ISR-side RX parsing while preserving mesh-mode selection.
	 */
	void serialbus_set_rx_accepting_input(bool enabled);

	/**
	 * Advance the ISR RX parser idle timer by one TCB2 tick.
	 */
	void serialbus_rx_idle_tick(void);

	/**
	 * Stop any active transmission and reset transmit state.
	 */
	void serialbus_end_tx(void);

	/**
	 */
	// void serialbus_reset_rx(void);

	/**
	 * Retrieve the next available empty transmit buffer or null if none.
	 */
	SerialbusTxBuffer *nextEmptySBTxBuffer(void);

	/**
	 * Obtain the next transmit buffer that contains data.
	 */
	SerialbusTxBuffer *nextFullSBTxBuffer(void);

	/**
	 * Returns true while the UART is currently sending bytes.
	 */
	bool serialbusTxInProgress(void);

	/**
	 * Begin transmission of the next queued serial-bus message if the UART is idle.
	 *
	 * @return true when transmission was started, false if a transmission is already active.
	 */
	bool serialbus_start_tx(void);

	/**
	 * Fetch the next empty receive buffer for incoming data.
	 */
	SerialbusRxBuffer *nextEmptySBRxBuffer(void);

	/**
	 * Get the next receive buffer that has been filled with a message.
	 */
	SerialbusRxBuffer *nextFullSBRxBuffer(void);

	/**
	 * Queue a new command prompt on the serial interface.
	 */
	void sb_send_NewPrompt(void);

	/**
	 * Send a newline sequence to the serial bus.
	 */
	void sb_send_NewLine(void);

	/**
	 * Echo a character back to the host terminal.
	 */
	void sb_echo_char(uint8_t c);

	/**
	 * Queue a single echo character from ISR context without blocking.
	 *
	 * @param c Character to echo.
	 * @return true when the character was queued successfully.
	 */
	bool sb_echo_char_isr(uint8_t c);

	/**
	 * Pop one pending ISR-queued echo character.
	 *
	 * @param c Destination for the queued character.
	 * @return true when a character was returned.
	 */
	bool serialbus_echo_try_get_isr(uint8_t *c);

	/**
	 * Queue a string for transmission using normal caller routing.
	 *
	 * @param str Null-terminated string to send.
	 * @return true on error, false on success.
	 */
	bool sb_send_string(char *str);

	/**
	 * Queue a string for transmission without the non-master forwarding shortcut.
	 *
	 * @param str Null-terminated string to send.
	 * @return true on error, false on success.
	 */
	bool sb_send_master_string(char *str);

	/**
	 * Send an ASCII label followed by a numeric value.
	 */
	void sb_send_value(uint16_t value, char *label);

	/**
	 * Returns true when the serial bus has been initialized and enabled.
	 */
	bool sb_enabled(void);

#ifdef __cplusplus
}
#endif

#endif /* SERIALBUS_H_ */
