OpenARDF/SignalSlinger/Software/AVR128DA28/SignalSlinger/include/external_battery_feedback.h

#ifndef EXTERNAL_BATTERY_FEEDBACK_H
#define EXTERNAL_BATTERY_FEEDBACK_H

#include <stdint.h>

/* Awake-only requests for the existing ADC scheduler. TCB0 runs at 300 Hz
 * (24 MHz / 2 / 40000); the legacy TIMER2_* names describe a different timer.
 * The controller never performs a conversion or changes transmission state.
 */
class ExternalBatteryFeedback
{
public:
    static const uint16_t TICKS_PER_SECOND = 300;
    static const uint16_t SETTLE_TICKS = 3; // At least 10 ms after requesting power.
    static const uint16_t VISIBLE_INTERVAL = TICKS_PER_SECOND;
    static const uint16_t PROBE_INTERVAL = 10 * TICKS_PER_SECOND;
    static const uint16_t BACKGROUND_INTERVAL = 8 * TICKS_PER_SECOND;
    static const uint16_t REQUEST_TIMEOUT = TICKS_PER_SECOND / 10;

    void reset()
    {
        initialized_ = visible_ = powered_ = managed_ = pending_ = probe_ = false;
        settle_ = age_ = remaining_ = 0;
    }

    void tick(bool awake, bool visible, bool managed, bool powerRequested)
    {
        if(!awake)
        {
            reset();
            return;
        }

        // With battery control disabled, the auxiliary output may be a fan.
        // Sample the directly connected supply without touching that output.
        bool powered = !managed || powerRequested;
        bool refresh = !initialized_ || (visible && !visible_) || (powered && !powered_);
        bool becameDark = initialized_ && !visible && visible_;
        bool changedMode = initialized_ && managed != managed_;
        initialized_ = true;
        visible_ = visible;
        powered_ = powered;
        managed_ = managed;
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
